Semi-ATE/PCB-Tester/hardware/mechanics/solidworks/2019SP3.0/PCB-Relay-Board/README.md

# PCB-Relay-Board

This directory holds the 3D model of the PCB-Relay-Board (extracted from Altium, or maunally made in solidworks)
