Semi-ATE/PCB-Tester/hardware/mechanics/solidworks/2019SP3.0/PCB-Tester-Board/Raspberry Pi 4B/RPI4B.SLDASM

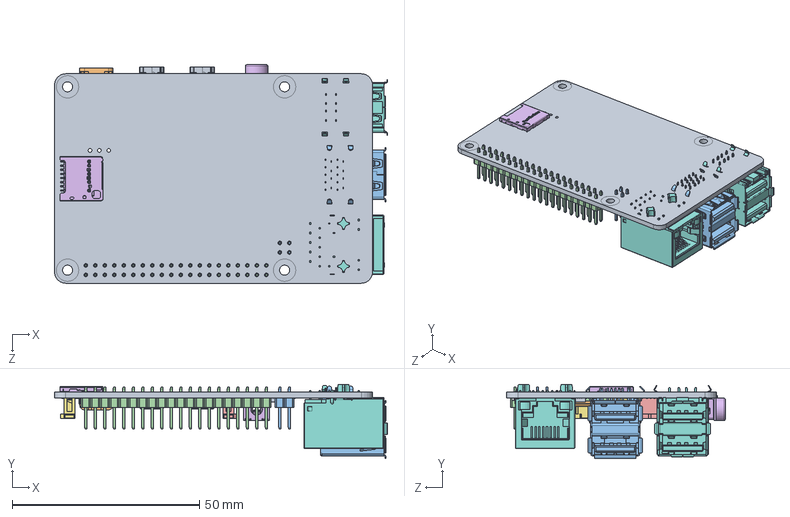
[picture p20: CAD file, 2020-09-08]
hardware/mechanics/solidworks/2019SP3.0/PCB-Tester-Board/Raspberry Pi 4B/RPI4B.SLDASM
89.0 x 19.9 x 58.4 mm
PCB, RPi4ModelB
Broadcom BCM2711B0 CPU, RPi4ModelB
2.54 mm DUPONT MALE PIN HEADER, POE, 2X2, RPi4ModelB
2.54 mm DUPONT MALE PIN HEADER, IO, 2X20, RPi4ModelB
Camera Connector, RPi4ModelB
Microphone Plug, RPi4ModelB
Display Connector, RPi4ModelB
Gigabit Ethernet Port, RPi4ModelB
Female Micro HDMI Connector, RPi4ModelB x 2
Female USB Type C Connector, RPi4ModelB
2X USB3.0 PORTS, RPi4ModelB
91D77 D9WHV 778K, 4 GB LPDDR4 SDRAM, RPi4ModelB
Cypress CYW43455 Wireless Module Cover, RPi4ModelB
SD Card Slot, RPi4ModelB
VIA VL805 PCIe USB 3.0 controller, RPi4ModelB
2X USB2.0 PORTS, RPi4ModelB
Broadcom BCM54213PE Gigabit Ethernet Transceiver, RPi4ModelB
MxL7704 Universal PMIC, RPi4ModelB
