Semi-ATE/PCB-Tester/hardware/mechanics/solidworks/2019SP3.0/housing/Lever_top.SLDASM

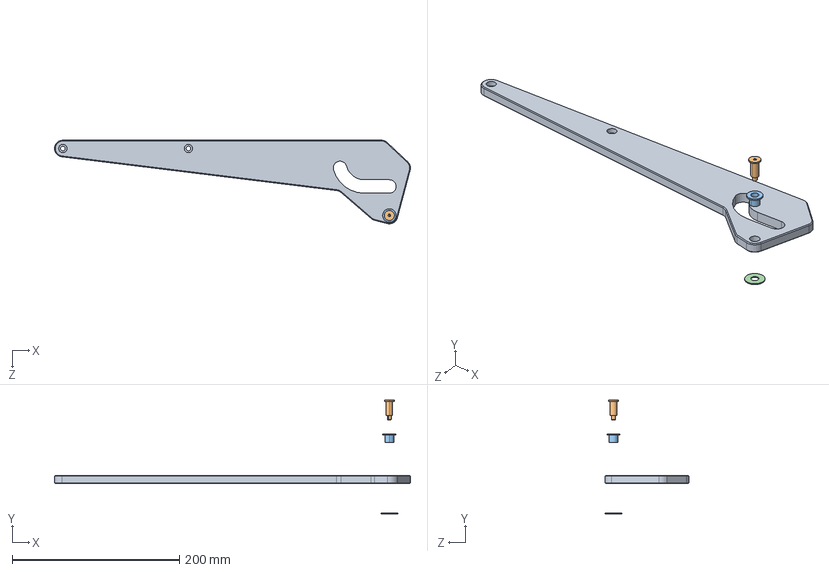
[picture p21: CAD file, 2020-09-08]
hardware/mechanics/solidworks/2019SP3.0/housing/Lever_top.SLDASM
425.2 x 135.8 x 100.0 mm
Lever_top_right
DBGB5-17-5
FWHJ-D10.5-H16.0-V8.0-T1.5-L10.0
SWSJJ20-8-1
