Semi-ATE/PCB-Tester/hardware/mechanics/solidworks/2019SP3.0/housing/Housing.SLDASM

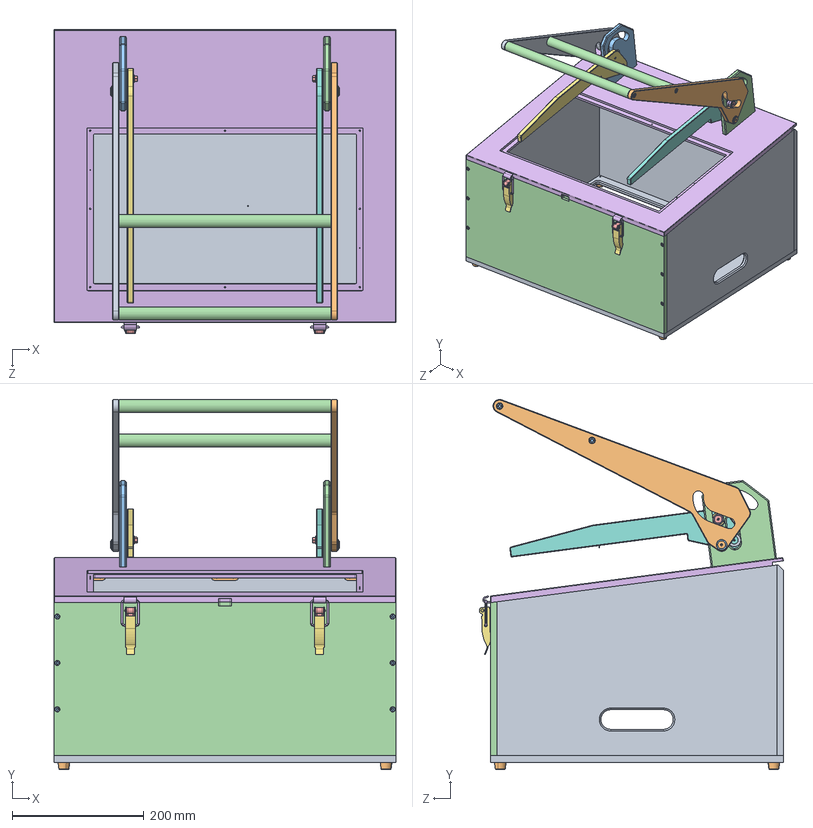
[picture p22: CAD file, 2020-09-08]
hardware/mechanics/solidworks/2019SP3.0/housing/Housing.SLDASM
520.0 x 562.6 x 463.0 mm
Housing_bottom
C-30-RK-18-black x 4
socket head cap screw_iso x 48
Housing_front
420111_base x 2
420111_eye x 2
420111_lever x 2
slotted cheese head screw_iso x 10
Housing_back
SHPSNA5_3 x 3
SHPSNA5_7 x 3
SHPSNA5_5 x 3
hex thin nut gradeb_iso x 6
Housing_top
Lever_bottom_left
Lever_bottom_right
Lever_top_left
Lever_top_right
Spindlehouse_left
Spindlehouse_right
DBGB5-20-10 x 2
B688ZZ x 10
SWSJJ20-8-1 x 6
DBGB5-15-10 x 2
FWHJ-D16.0-H20.0-V8.0-T1.5-L4.0 x 2
DBGB5-17-5 x 2
FWHJ-D10.5-H16.0-V8.0-T1.5-L10.0 x 2
Handle x 2
FRNUT5 x 2
420111_hook x 2
pan head cross recess screw_iso x 4
parallel pin hardened_iso x 4
Housing_side x 2
