Semi-ATE/PCB-Tester/hardware/mechanics/solidworks/2019SP3.0/housing/Spindle3.SLDASM

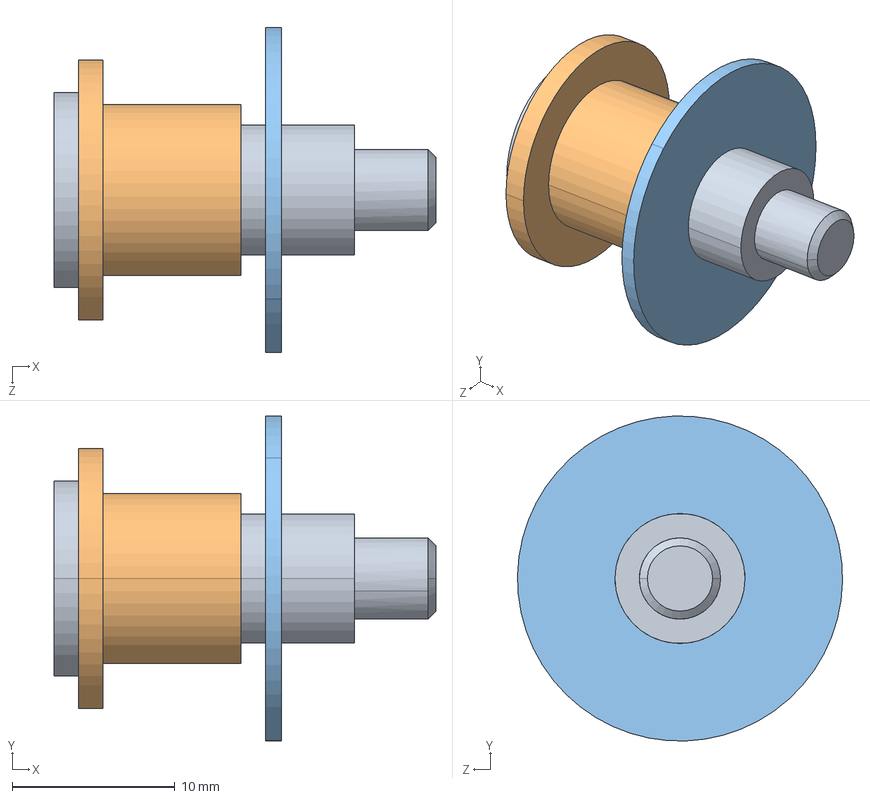
[picture p23: CAD file, 2020-09-08]
hardware/mechanics/solidworks/2019SP3.0/housing/Spindle3.SLDASM
23.5 x 20.0 x 20.0 mm
DBGB5-17-5
FWHJ-D10.5-H16.0-V8.0-T1.5-L10.0
SWSJJ20-8-1
