Semi-ATE/PCB-Tester/hardware/mechanics/solidworks/2019SP3.0/housing/Spindle2.SLDASM

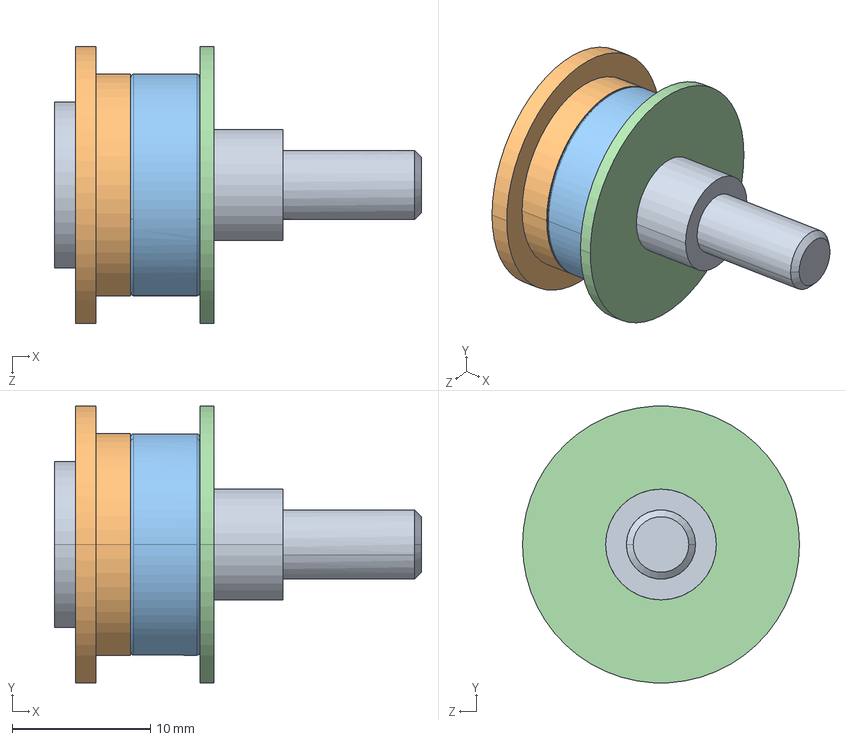
[picture p24: CAD file, 2020-09-08]
hardware/mechanics/solidworks/2019SP3.0/housing/Spindle2.SLDASM
26.5 x 20.0 x 20.0 mm
DBGB5-15-10
FWHJ-D16.0-H20.0-V8.0-T1.5-L4.0
B688ZZ
SWSJJ20-8-1
