Semi-ATE/PCB-Tester/hardware/mechanics/solidworks/2019SP3.0/housing/Lever_bottom.SLDASM

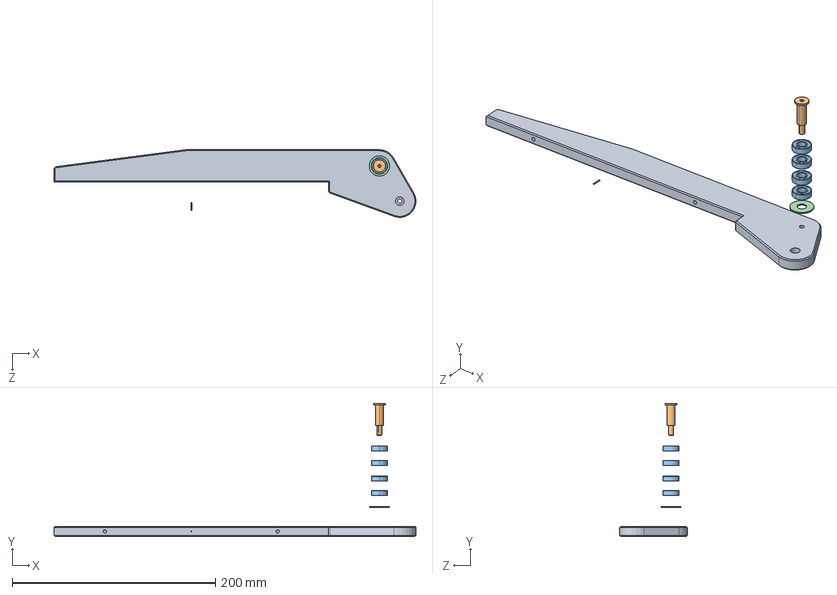
[picture p25: CAD file, 2020-09-08]
hardware/mechanics/solidworks/2019SP3.0/housing/Lever_bottom.SLDASM
356.0 x 130.8 x 66.6 mm
Lever_bottom_right
DBGB5-20-10
B688ZZ x 4
SWSJJ20-8-1
parallel pin hardened_iso
