Semi-ATE/PCB-Tester/hardware/mechanics/solidworks/2019SP3.0/housing/Spindle1.SLDASM

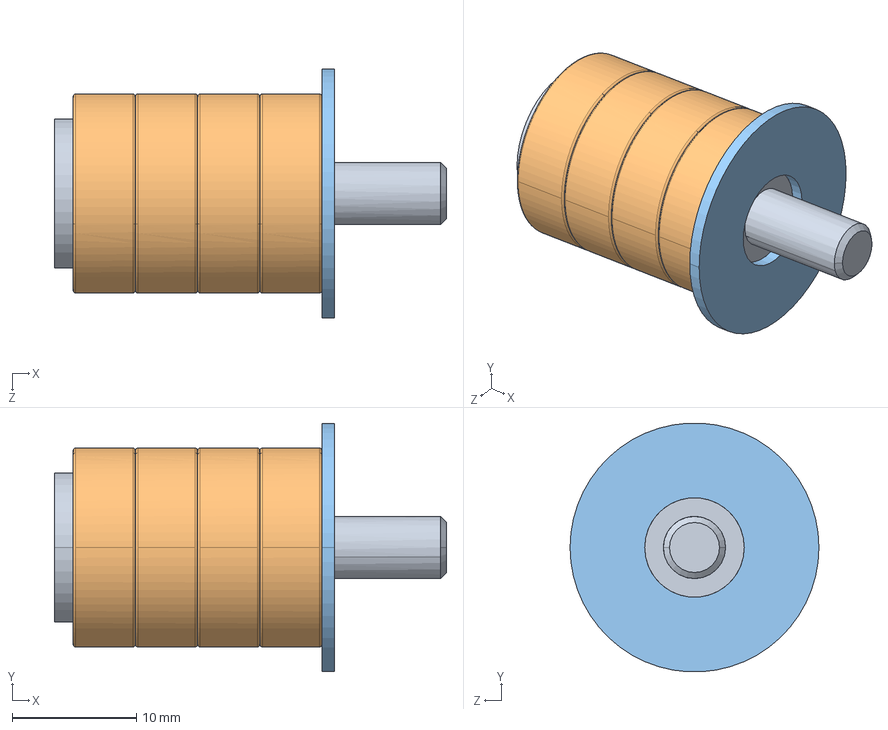
[picture p26: CAD file, 2020-09-08]
hardware/mechanics/solidworks/2019SP3.0/housing/Spindle1.SLDASM
31.5 x 20.0 x 20.0 mm
DBGB5-20-10
B688ZZ x 4
SWSJJ20-8-1
