Semi-ATE/PCB-Tester/hardware/mechanics/solidworks/2019SP3.0/housing/Spindlehouse.SLDASM

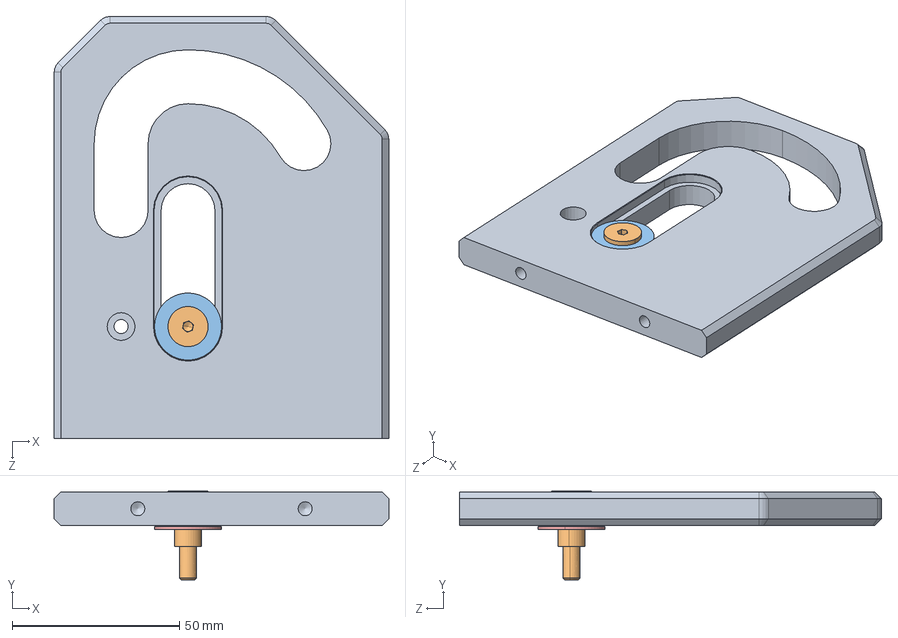
[picture p27: CAD file, 2020-09-08]
hardware/mechanics/solidworks/2019SP3.0/housing/Spindlehouse.SLDASM
100.0 x 26.5 x 126.1 mm
Spindlehouse_right
DBGB5-15-10
FWHJ-D16.0-H20.0-V8.0-T1.5-L4.0
B688ZZ
SWSJJ20-8-1
