Semi-ATE/PCB-Tester/hardware/electronics/altium/20.1.12/PCB-Tester-Board/Parts/SupportPost.STEP

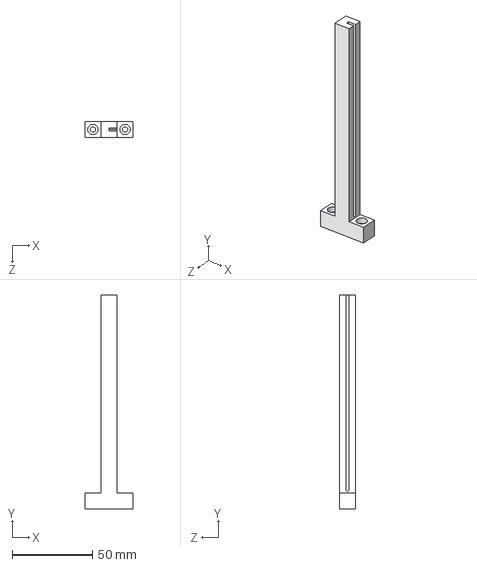
[picture p28: CAD file, 2020-09-08]
hardware/electronics/altium/20.1.12/PCB-Tester-Board/Parts/SupportPost.STEP
30.0 x 133.0 x 10.0 mm
