Semi-ATE/PCB-Tester/hardware/electronics/altium/20.1.12/PCB-Tester-Board/PCB-Tester-Board.DXF

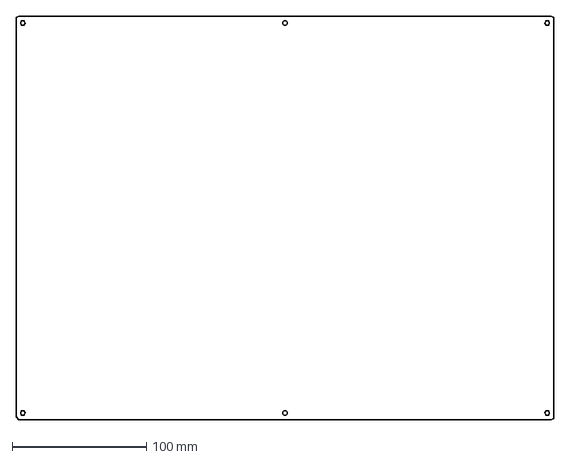
[picture p29: CAD file, 2020-04-20]
hardware/electronics/altium/20.1.12/PCB-Tester-Board/PCB-Tester-Board.DXF
400.0 x 300.0 mm
