Semi-ATE/PCB-Tester/hardware/electronics/altium/20.1.12/PCB-Tester-Relay-Board/Board-Outline.DXF

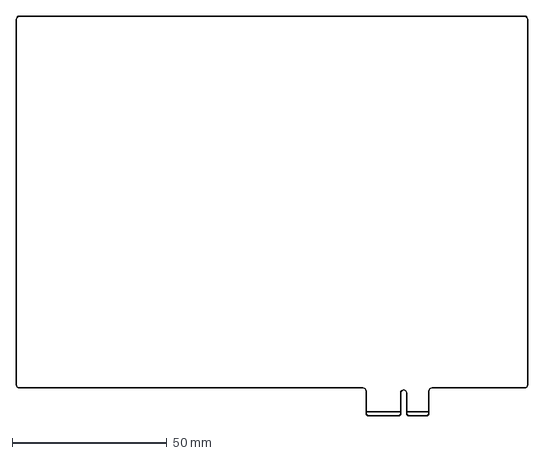
[picture p30: CAD file, 2020-04-20]
hardware/electronics/altium/20.1.12/PCB-Tester-Relay-Board/Board-Outline.DXF
165.0 x 129.0 mm
