Semi-ATE/PCB-Tester/hardware/mechanics/solidworks/2019SP3.0/housing/A22NE-M-PD22-N/A22NE_M_N_BASE.SLDPRT

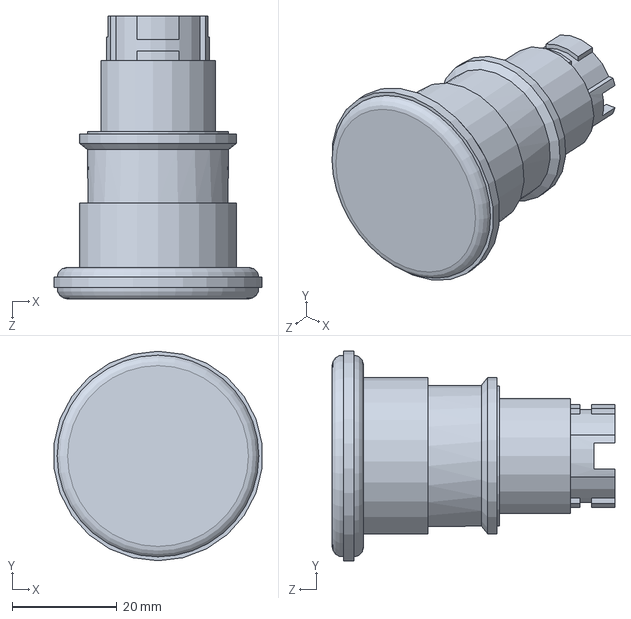
[picture p31: CAD file, 2020-09-11]
hardware/mechanics/solidworks/2019SP3.0/housing/A22NE-M-PD22-N/A22NE_M_N_BASE.SLDPRT
39.7 x 40.0 x 54.0 mm
