Semi-ATE/PCB-Tester/hardware/mechanics/solidworks/2019SP3.0/HUMAN BODY.SLDPRT

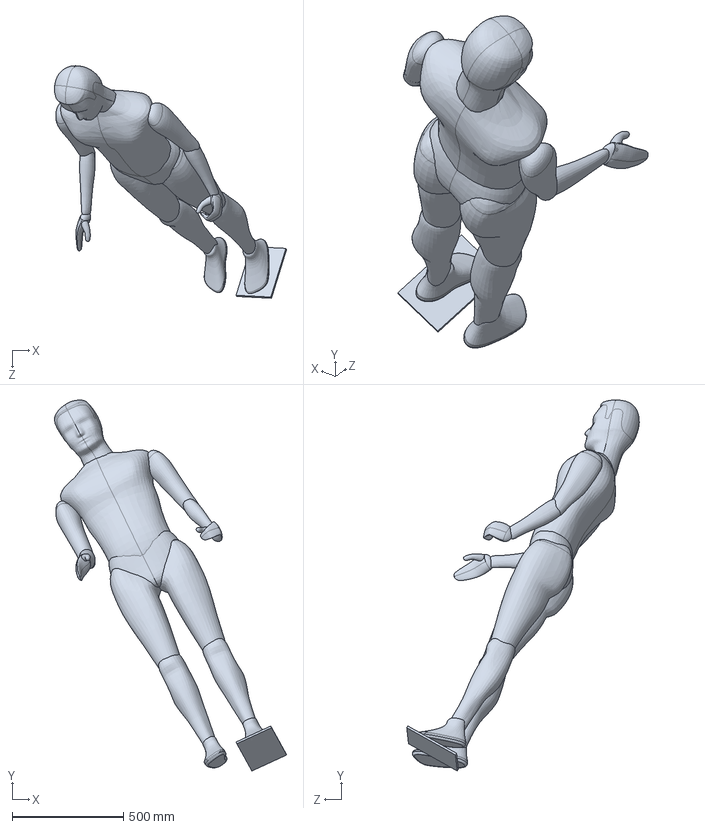
[picture p32: CAD file, 2020-09-08]
hardware/mechanics/solidworks/2019SP3.0/HUMAN BODY.SLDPRT
1042.4 x 1665.2 x 1043.8 mm
