Semi-ATE/PCB-Tester/hardware/mechanics/solidworks/2019SP3.0/PCB-Relay-Board/TFC-132-01-F-D-RA/_TFC_132_01_L_D_RA_terminal_2.sldprt

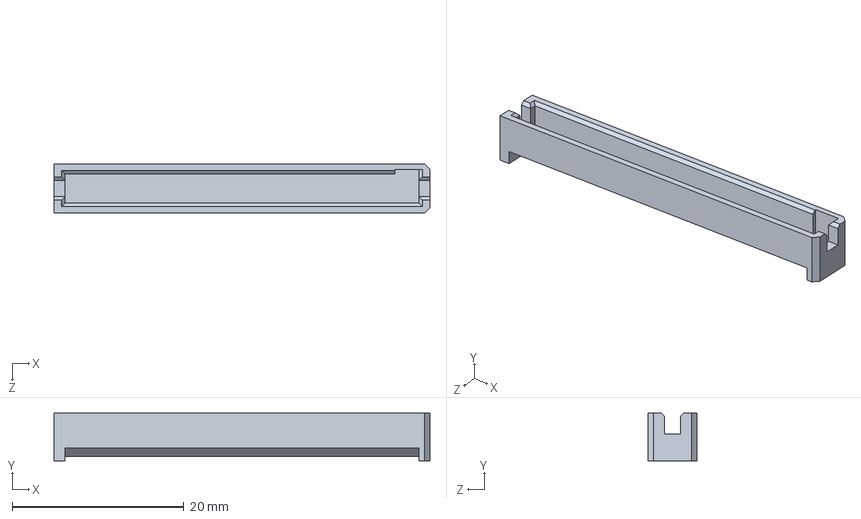
[picture p33: CAD file, 2020-04-20]
hardware/mechanics/solidworks/2019SP3.0/PCB-Relay-Board/TFC-132-01-F-D-RA/_TFC_132_01_L_D_RA_terminal_2.sldprt
43.8 x 5.59 x 5.72 mm
