Semi-ATE/PCB-Tester/hardware/mechanics/solidworks/2019SP3.0/PCB-Tester-Board/118-1-A/118-1-A.SLDPRT

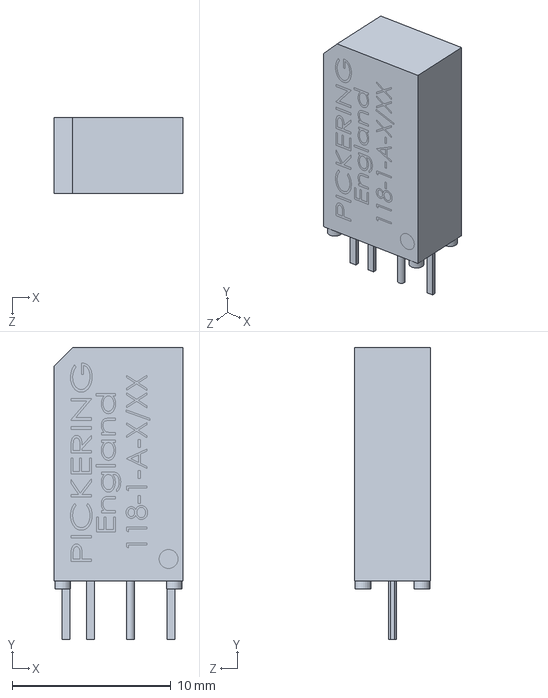
[picture p34: CAD file, 2020-09-08]
hardware/mechanics/solidworks/2019SP3.0/PCB-Tester-Board/118-1-A/118-1-A.SLDPRT
8.13 x 18.4 x 4.80 mm
