Semi-ATE/PCB-Tester/hardware/mechanics/solidworks/2019SP3.0/PCB-Tester-Board/1731721/pxc_1731721_05_GMKDS-3-2-7-62_3D.stp

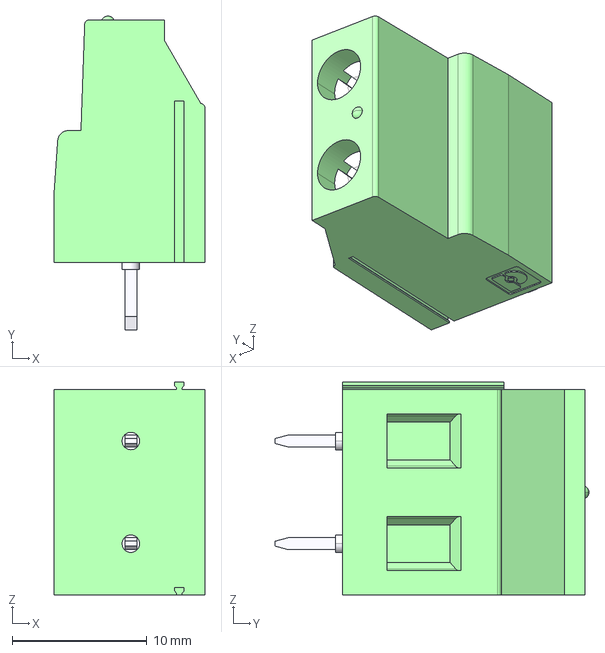
[picture p35: CAD file, 2020-09-08]
hardware/mechanics/solidworks/2019SP3.0/PCB-Tester-Board/1731721/pxc_1731721_05_GMKDS-3-2-7-62_3D.stp
11.2 x 23.3 x 15.8 mm
