Semi-ATE/PCB-Tester/hardware/mechanics/solidworks/2019SP3.0/PCB-Tester-Board/ASE-25.000MHZ-LC-T/ASE.STEP

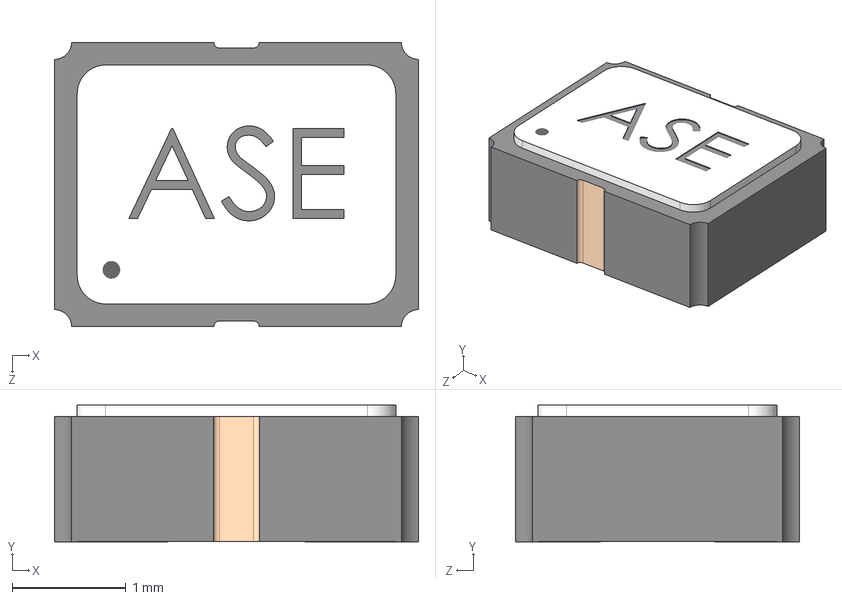
[picture p36: CAD file, 2020-04-20]
hardware/mechanics/solidworks/2019SP3.0/PCB-Tester-Board/ASE-25.000MHZ-LC-T/ASE.STEP
3.20 x 1.20 x 2.50 mm
