Semi-ATE/PCB-Tester/hardware/mechanics/solidworks/2019SP3.0/PCB-Tester-Board/B6PS-VH/VHR-6N.SLDPRT

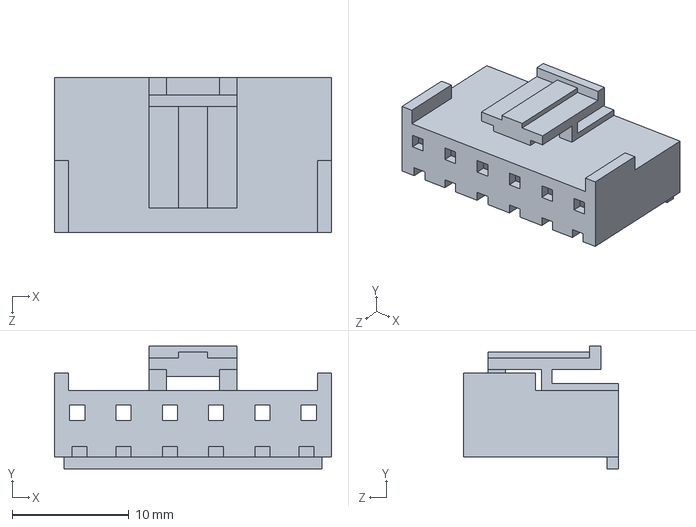
[picture p37: CAD file, 2020-09-08]
hardware/mechanics/solidworks/2019SP3.0/PCB-Tester-Board/B6PS-VH/VHR-6N.SLDPRT
23.7 x 10.5 x 13.3 mm
