Semi-ATE/PCB-Tester/hardware/mechanics/solidworks/2019SP3.0/PCB-Tester-Board/G3VM-61A1/G3VM_61A1.STEP

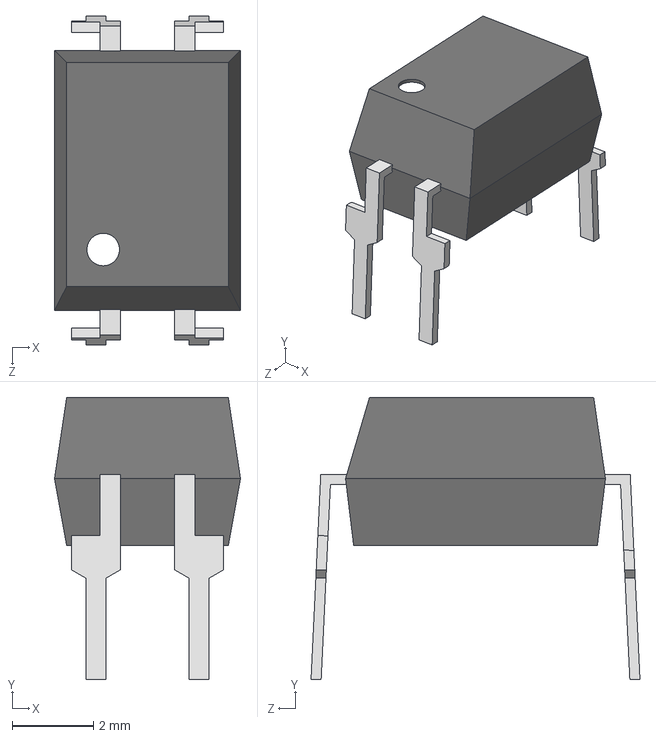
[picture p38: CAD file, 2020-04-20]
hardware/mechanics/solidworks/2019SP3.0/PCB-Tester-Board/G3VM-61A1/G3VM_61A1.STEP
4.58 x 6.95 x 8.10 mm
