Semi-ATE/PCB-Tester/hardware/mechanics/solidworks/2019SP3.0/PCB-Tester-Board/HF118F005-1ZS1/HF118F005-1ZS1.STEP

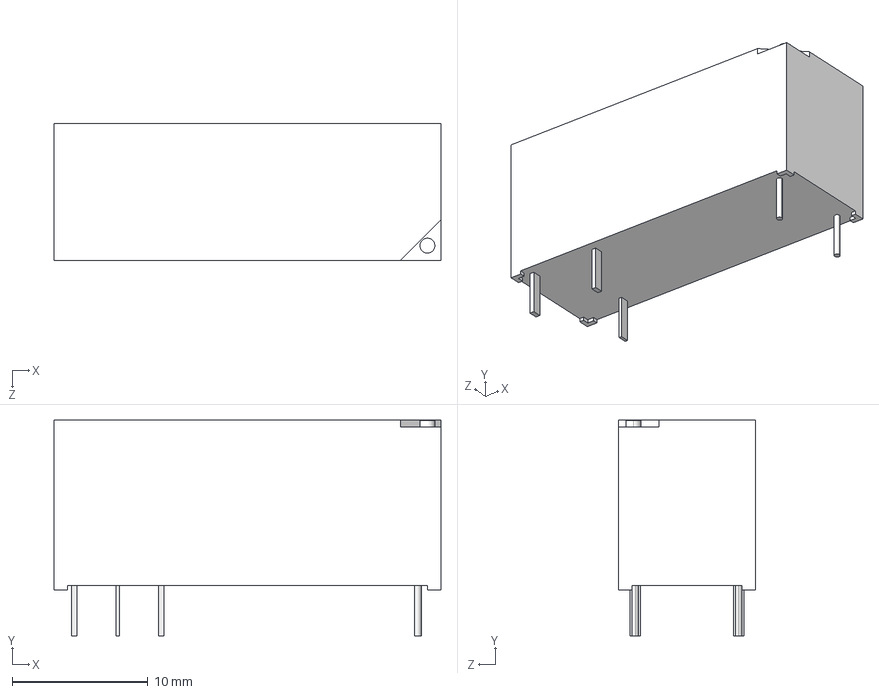
[picture p39: CAD file, 2020-04-20]
hardware/mechanics/solidworks/2019SP3.0/PCB-Tester-Board/HF118F005-1ZS1/HF118F005-1ZS1.STEP
28.5 x 15.9 x 10.1 mm
