Semi-ATE/PCB-Tester/hardware/mechanics/solidworks/2019SP3.0/PCB-Tester-Board/PCB-Tester-PCB.SLDPRT

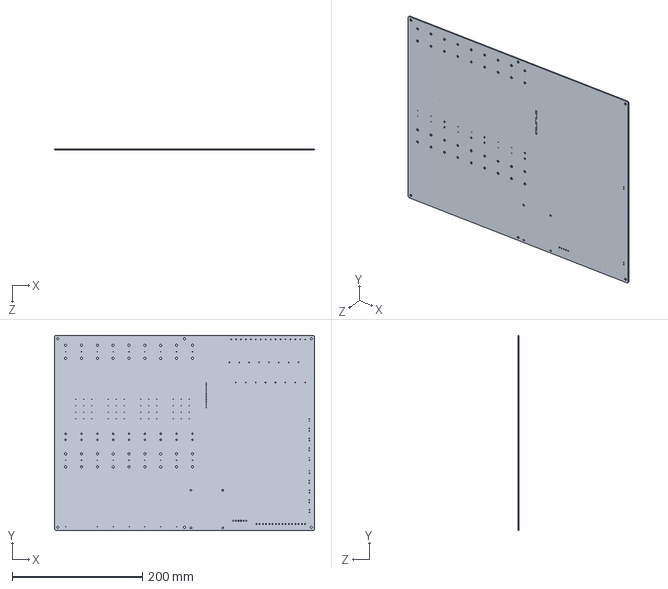
[picture p40: CAD file, 2020-09-08]
hardware/mechanics/solidworks/2019SP3.0/PCB-Tester-Board/PCB-Tester-PCB.SLDPRT
400.0 x 300.0 x 1.60 mm
