Semi-ATE/PCB-Tester/hardware/mechanics/solidworks/2019SP3.0/PCB-Tester-Board/TFC-132-01-F-D-LC/TFC-132-01-F-D-LC.STEP

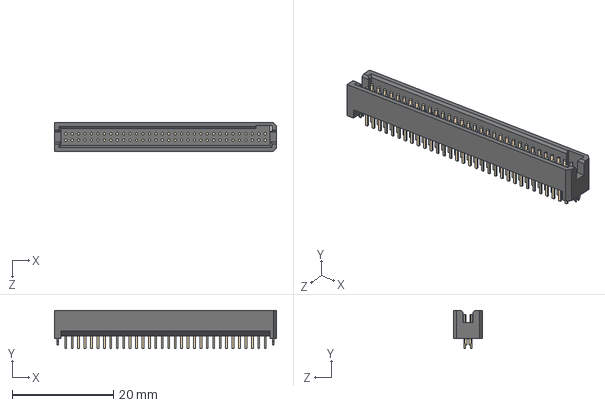
[picture p42: CAD file, 2020-04-20]
hardware/mechanics/solidworks/2019SP3.0/PCB-Tester-Board/TFC-132-01-F-D-LC/TFC-132-01-F-D-LC.STEP
43.8 x 7.57 x 5.71 mm
_TFC_132_01_L_D_LC_terminal_2
_TFC_132_01_L_D_pins_4
