Semi-ATE/PCB-Tester/hardware/mechanics/solidworks/2019SP3.0/PCB-Tester-Board/TSR 2-2450/TSR2-2405.STEP

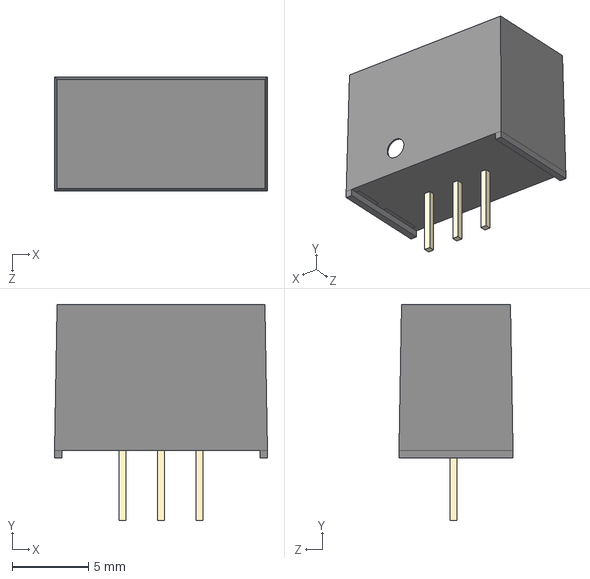
[picture p43: CAD file, 2020-04-20]
hardware/mechanics/solidworks/2019SP3.0/PCB-Tester-Board/TSR 2-2450/TSR2-2405.STEP
14.0 x 14.2 x 7.50 mm
