Semi-ATE/PCB-Tester/hardware/electronics/altium/20.1.12/PCB-Tester-Board/Parts/SupportBlock.STEP

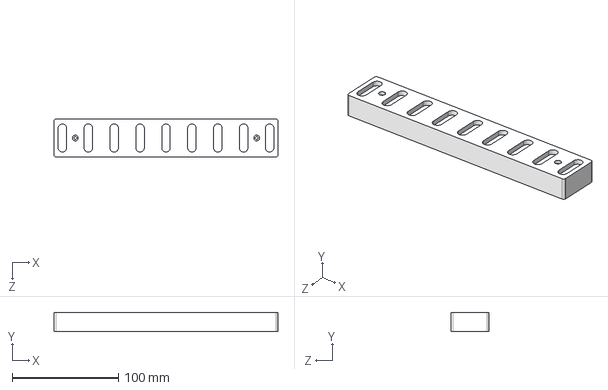
[picture p44: CAD file, 2020-09-08]
hardware/electronics/altium/20.1.12/PCB-Tester-Board/Parts/SupportBlock.STEP
211.0 x 18.0 x 36.0 mm
