Semi-ATE/PCB-Tester/hardware/mechanics/solidworks/2019SP3.0/housing/Housing_side.STEP

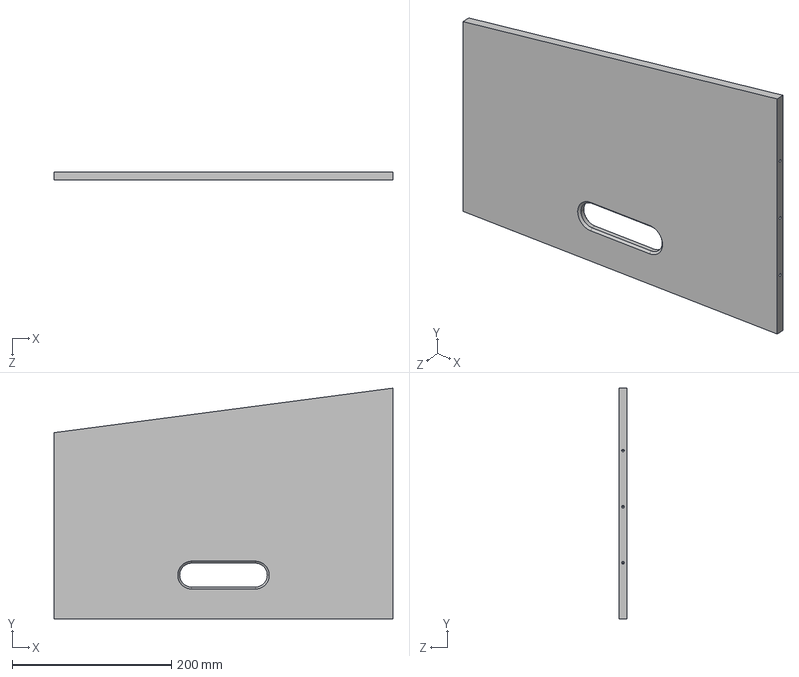
[picture p45: CAD file, 2020-09-11]
hardware/mechanics/solidworks/2019SP3.0/housing/Housing_side.STEP
426.0 x 290.0 x 10.0 mm
