Semi-ATE/PCB-Tester/hardware/mechanics/solidworks/2019SP3.0/housing/NP8E2D203QE/NP8E2D203QE_3.sldprt

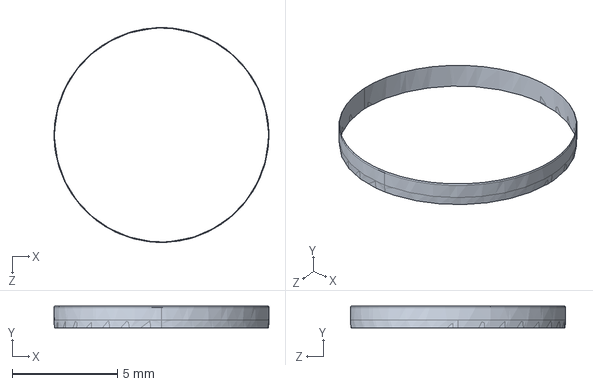
[picture p46: CAD file, 2020-09-11]
hardware/mechanics/solidworks/2019SP3.0/housing/NP8E2D203QE/NP8E2D203QE_3.sldprt
10.2 x 1.03 x 10.2 mm
