Semi-ATE/PCB-Tester/hardware/mechanics/solidworks/2019SP3.0/PCB-Relay-Board/PCB-Relay-PCB.SLDPRT

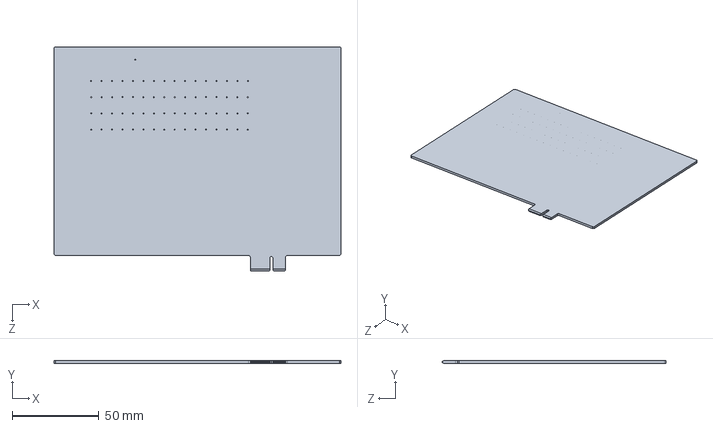
[picture p47: CAD file, 2020-09-08]
hardware/mechanics/solidworks/2019SP3.0/PCB-Relay-Board/PCB-Relay-PCB.SLDPRT
165.0 x 1.60 x 129.0 mm
