Semi-ATE/PCB-Tester/hardware/mechanics/solidworks/2019SP3.0/PCB-Relay-Board/SFSD-32-30C-G-15.00-S/_SFSD_32_28_D_NUS_ca_4.sldprt

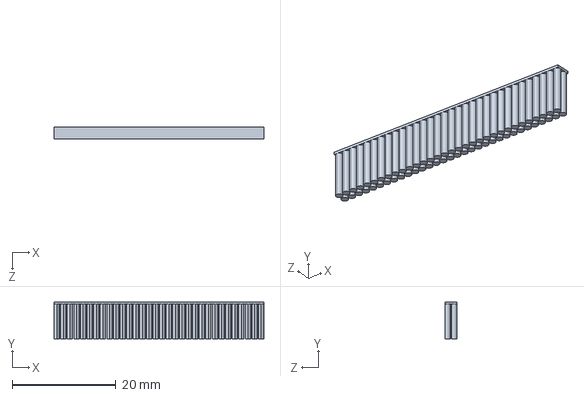
[picture p48: CAD file, 2020-04-20]
hardware/mechanics/solidworks/2019SP3.0/PCB-Relay-Board/SFSD-32-30C-G-15.00-S/_SFSD_32_28_D_NUS_ca_4.sldprt
40.4 x 7.11 x 2.34 mm
