Semi-ATE/PCB-Tester/hardware/mechanics/solidworks/2019SP3.0/PCB-Relay-Board/TFC-132-01-F-D-RA/TFC-132-01-F-D-RA.STEP

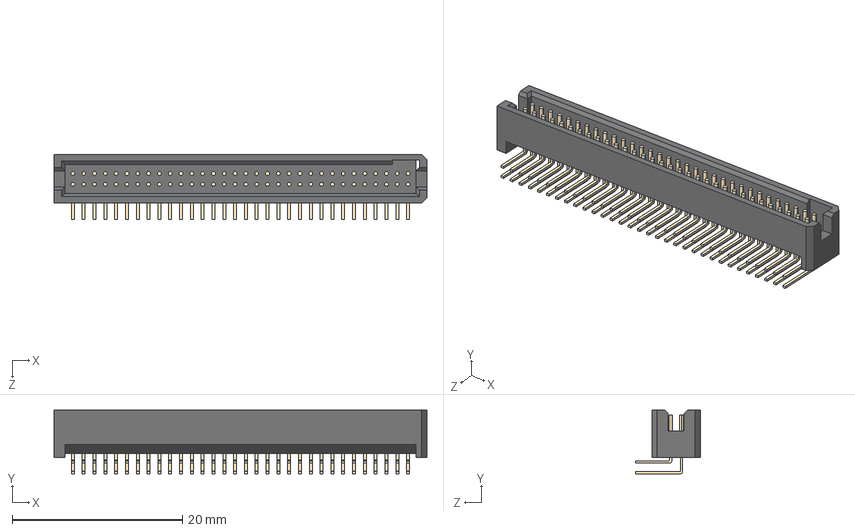
[picture p49: CAD file, 2020-04-20]
hardware/mechanics/solidworks/2019SP3.0/PCB-Relay-Board/TFC-132-01-F-D-RA/TFC-132-01-F-D-RA.STEP
43.8 x 7.49 x 7.62 mm
_TFC_132_01_L_D_RA_terminal_2
_TFC_132_01_L_D_RA_pins_4
