Semi-ATE/PCB-Tester/hardware/mechanics/solidworks/2019SP3.0/PCB-Tester-Board/M2.5x16 standoff/HSM2.5-6.4-16-2.STEP

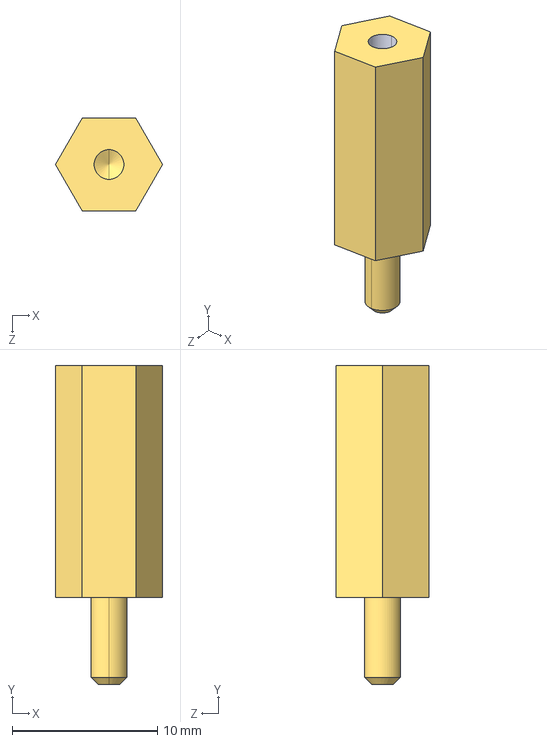
[picture p50: CAD file, 2020-04-20]
hardware/mechanics/solidworks/2019SP3.0/PCB-Tester-Board/M2.5x16 standoff/HSM2.5-6.4-16-2.STEP
7.39 x 22.0 x 6.40 mm
