Semi-ATE/PCB-Tester/hardware/mechanics/solidworks/2019SP3.0/PCB-Tester-Board/PCIE-036-02-F-D-TH/PCIE_036_02_F_D_TH_3.sldprt

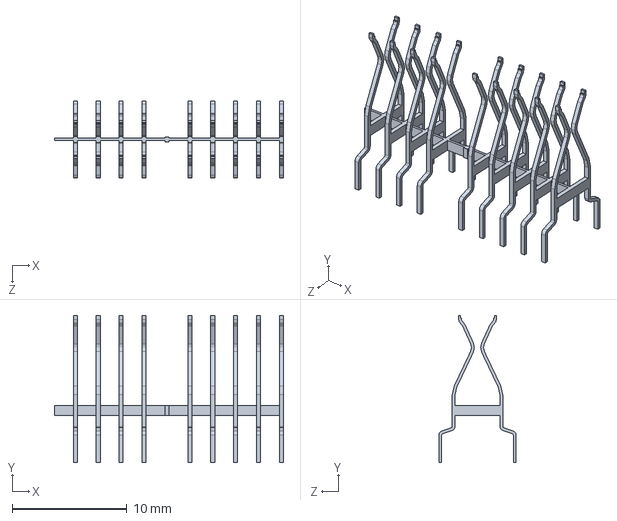
[picture p51: CAD file, 2020-09-08]
hardware/mechanics/solidworks/2019SP3.0/PCB-Tester-Board/PCIE-036-02-F-D-TH/PCIE_036_02_F_D_TH_3.sldprt
20.0 x 12.9 x 6.76 mm
