Semi-ATE/PCB-Tester/hardware/mechanics/solidworks/2019SP3.0/PCB-Tester-Board/TFC-132-01-F-D-LC/_TFC_132_01_L_D_LC_terminal_2.sldprt

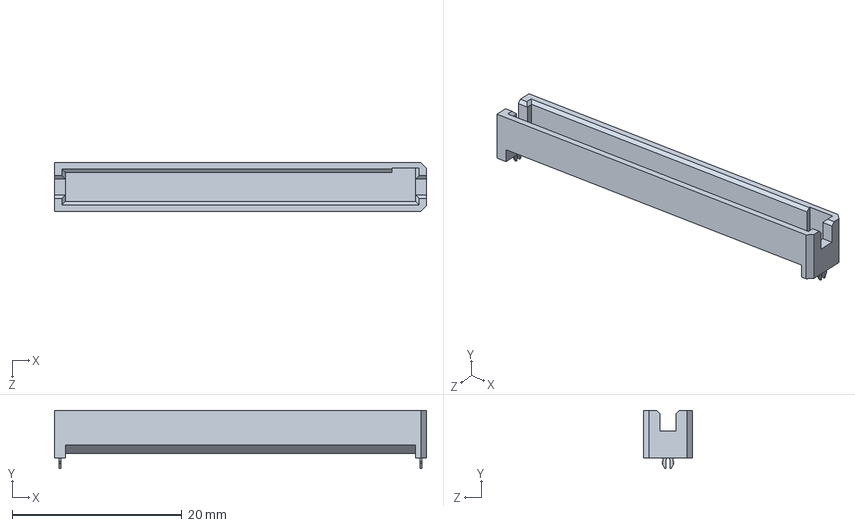
[picture p53: CAD file, 2020-04-20]
hardware/mechanics/solidworks/2019SP3.0/PCB-Tester-Board/TFC-132-01-F-D-LC/_TFC_132_01_L_D_LC_terminal_2.sldprt
43.8 x 6.86 x 5.72 mm
