Semi-ATE/PCB-Tester/hardware/mechanics/solidworks/2019SP3.0/housing/Housing_bottom.STEP

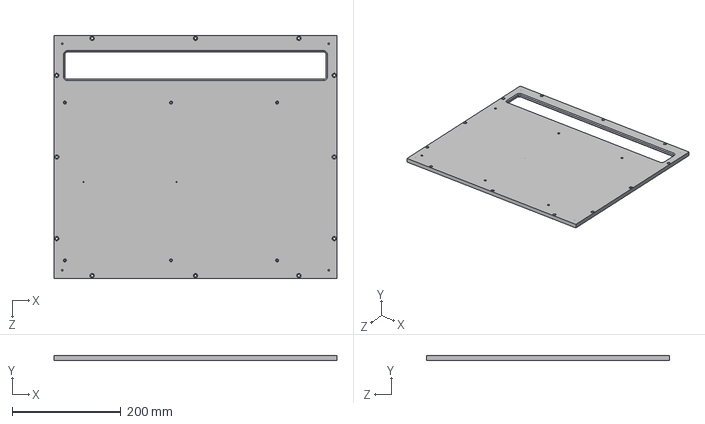
[picture p54: CAD file, 2020-09-11]
hardware/mechanics/solidworks/2019SP3.0/housing/Housing_bottom.STEP
520.0 x 10.0 x 446.0 mm
