Semi-ATE/PCB-Tester/hardware/mechanics/solidworks/2019SP3.0/PCB-Relay-Board/SFSD-32-30C-G-15.00-S/_SFSD_32_30_S_b_2.sldprt

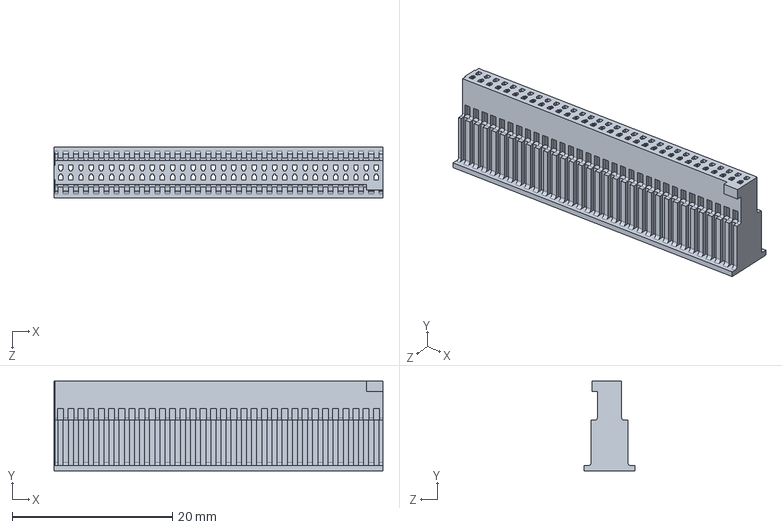
[picture p55: CAD file, 2020-04-20]
hardware/mechanics/solidworks/2019SP3.0/PCB-Relay-Board/SFSD-32-30C-G-15.00-S/_SFSD_32_30_S_b_2.sldprt
41.0 x 11.2 x 6.35 mm
