Semi-ATE/PCB-Tester/hardware/mechanics/solidworks/2019SP3.0/PCB-Relay-Board/TFC-132-01-F-D-RA/_TFC_132_01_L_D_RA_pins_4.sldprt

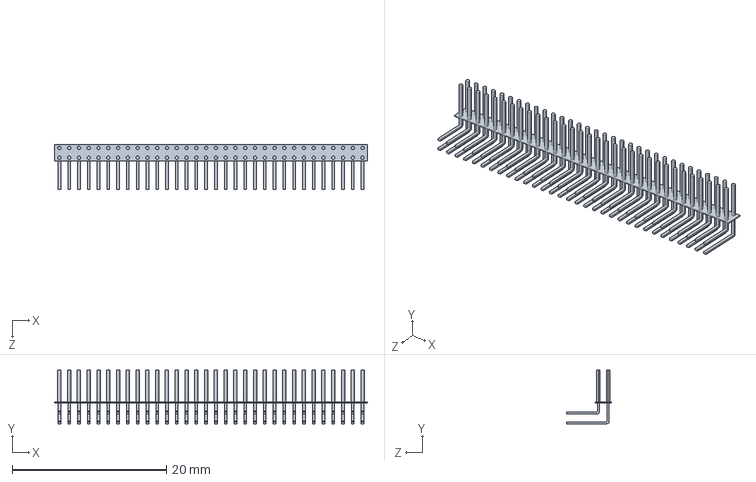
[picture p56: CAD file, 2020-04-20]
hardware/mechanics/solidworks/2019SP3.0/PCB-Relay-Board/TFC-132-01-F-D-RA/_TFC_132_01_L_D_RA_pins_4.sldprt
40.6 x 6.95 x 5.84 mm
