Semi-ATE/PCB-Tester/hardware/mechanics/solidworks/2019SP3.0/PCB-Tester-Board/TFC-132-01-F-D-LC/_TFC_132_01_L_D_pins_4.sldprt

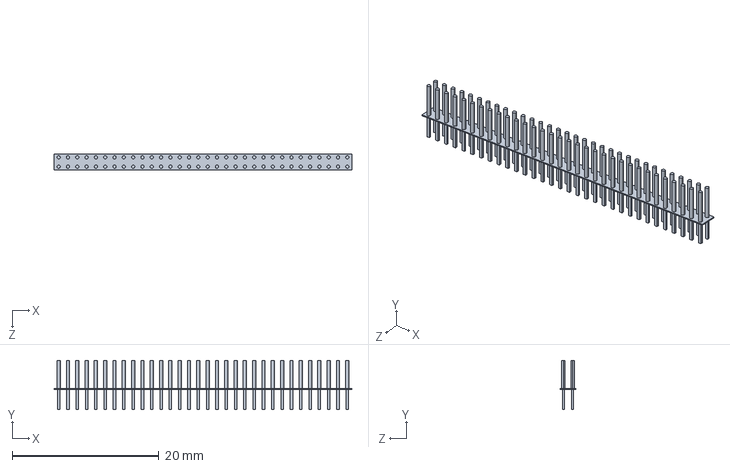
[picture p59: CAD file, 2020-04-20]
hardware/mechanics/solidworks/2019SP3.0/PCB-Tester-Board/TFC-132-01-F-D-LC/_TFC_132_01_L_D_pins_4.sldprt
40.6 x 6.74 x 2.16 mm
