Semi-ATE/PCB-Tester/hardware/mechanics/solidworks/2019SP3.0/housing/Housing_front.STEP

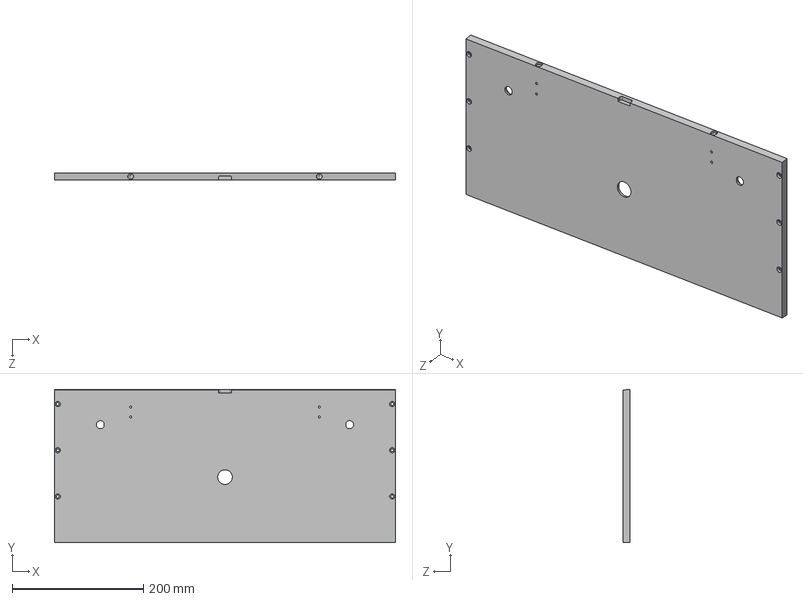
[picture p60: CAD file, 2020-09-11]
hardware/mechanics/solidworks/2019SP3.0/housing/Housing_front.STEP
520.0 x 234.0 x 10.0 mm
