Semi-ATE/PCB-Tester/hardware/mechanics/solidworks/2019SP3.0/housing/NP8E2D203QE/NP8E2D203QE_11.sldprt

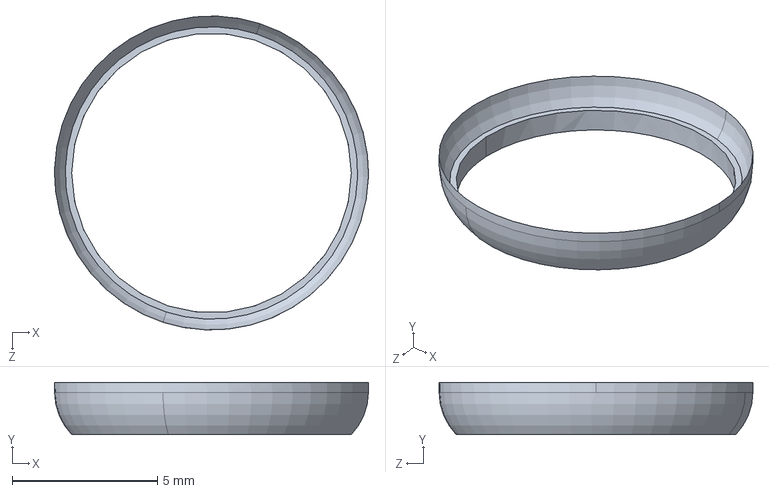
[picture p61: CAD file, 2020-09-11]
hardware/mechanics/solidworks/2019SP3.0/housing/NP8E2D203QE/NP8E2D203QE_11.sldprt
10.8 x 1.80 x 10.8 mm
