Semi-ATE/PCB-Tester/hardware/mechanics/solidworks/2019SP3.0/JIG/JBH6_10.sldprt

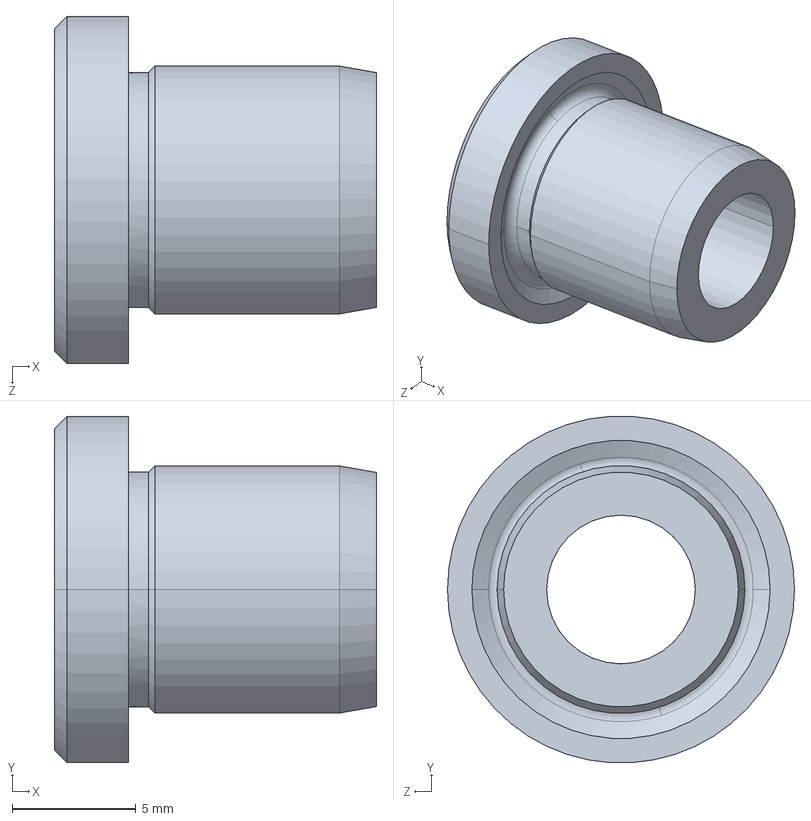
[picture p62: CAD file, 2020-09-08]
hardware/mechanics/solidworks/2019SP3.0/JIG/JBH6_10.sldprt
13.0 x 14.0 x 14.0 mm
