Semi-ATE/PCB-Tester/hardware/mechanics/solidworks/2019SP3.0/PCB-Relay-Board/SFSD-32-30C-G-15.00-S/_SFSD_32_p_6.sldprt

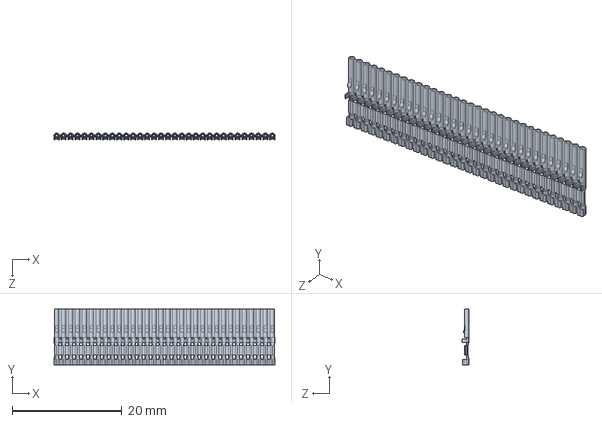
[picture p63: CAD file, 2020-04-20]
hardware/mechanics/solidworks/2019SP3.0/PCB-Relay-Board/SFSD-32-30C-G-15.00-S/_SFSD_32_p_6.sldprt
40.3 x 10.2 x 1.27 mm
