Semi-ATE/PCB-Tester/hardware/mechanics/solidworks/2019SP3.0/PCB-Tester-Board/PCIE-036-02-F-D-TH/PCIE_036_02_F_D_TH_7.sldprt

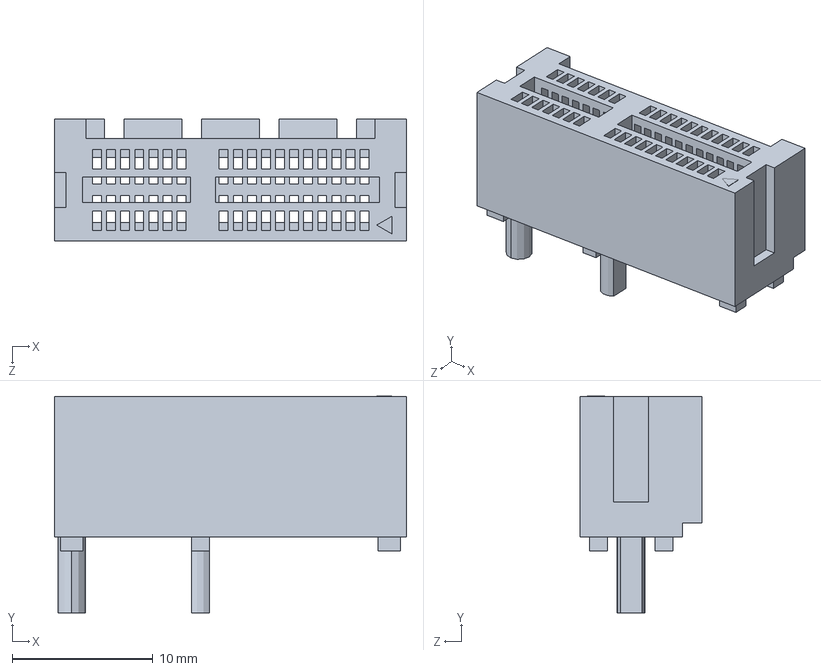
[picture p64: CAD file, 2020-09-08]
hardware/mechanics/solidworks/2019SP3.0/PCB-Tester-Board/PCIE-036-02-F-D-TH/PCIE_036_02_F_D_TH_7.sldprt
25.0 x 15.4 x 8.70 mm
