Semi-ATE/PCB-Tester/hardware/mechanics/solidworks/2019SP3.0/PCB-Tester-Board/Raspberry Pi 4B/2.54 mm DUPONT MALE PIN HEADER, IO, 2X20, RPi4ModelB.SLDPRT

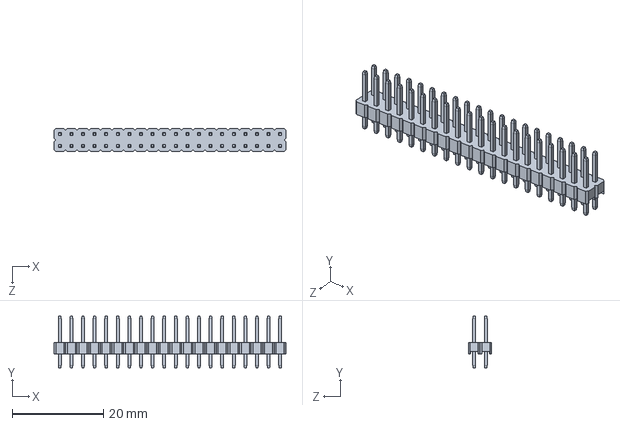
[picture p65: CAD file, 2020-09-08]
hardware/mechanics/solidworks/2019SP3.0/PCB-Tester-Board/Raspberry Pi 4B/2.54 mm DUPONT MALE PIN HEADER, IO, 2X20, RPi4ModelB.SLDPRT
50.8 x 11.3 x 5.08 mm
