Semi-ATE/PCB-Tester/hardware/mechanics/solidworks/2019SP3.0/housing/Housing_top.STEP

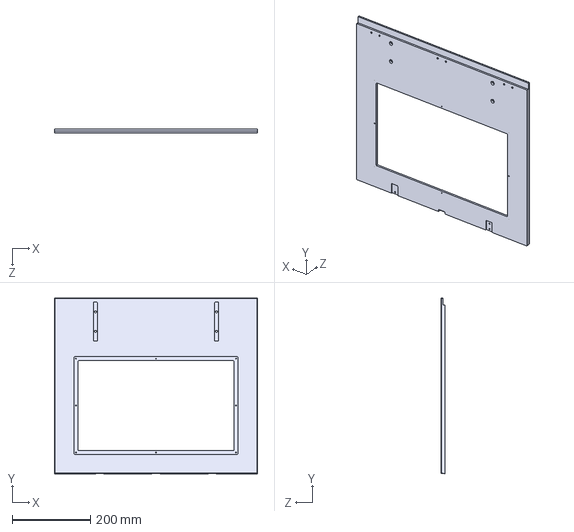
[picture p66: CAD file, 2020-09-11]
hardware/mechanics/solidworks/2019SP3.0/housing/Housing_top.STEP
520.0 x 450.0 x 10.0 mm
