Semi-ATE/PCB-Tester/hardware/mechanics/solidworks/2019SP3.0/PCB-Tester-Board/Raspberry Pi 4B/Broadcom BCM2711B0 CPU, RPi4ModelB.SLDPRT

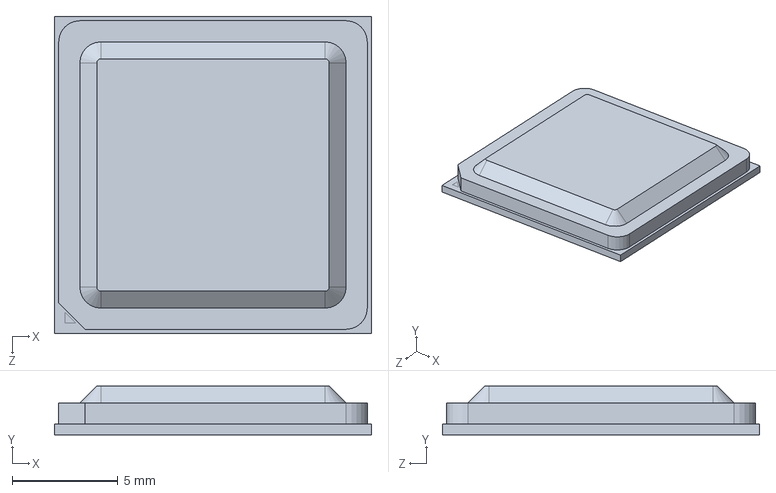
[picture p68: CAD file, 2020-09-08]
hardware/mechanics/solidworks/2019SP3.0/PCB-Tester-Board/Raspberry Pi 4B/Broadcom BCM2711B0 CPU, RPi4ModelB.SLDPRT
15.0 x 2.30 x 15.0 mm
