Semi-ATE/PCB-Tester/hardware/mechanics/solidworks/2019SP3.0/housing/A22NE-M-PD22-N/A22NE_M_PD22_N_LEVER.SLDPRT

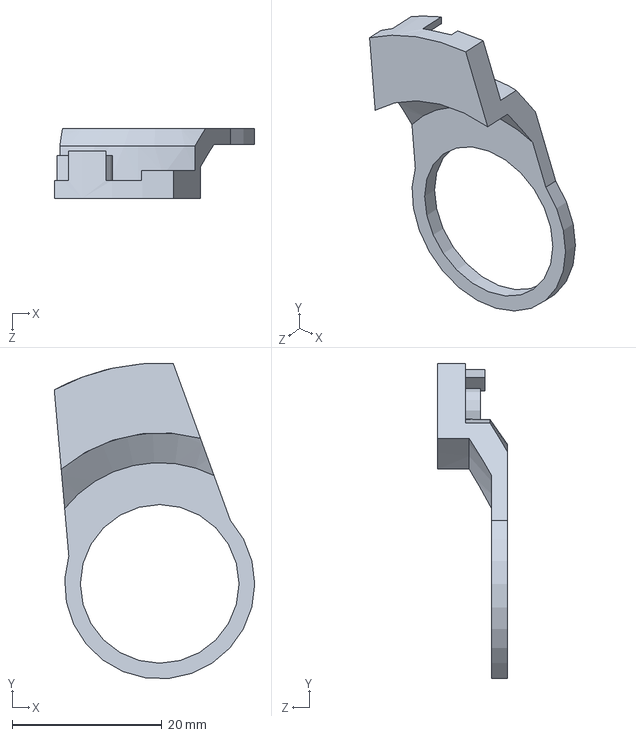
[picture p69: CAD file, 2020-09-11]
hardware/mechanics/solidworks/2019SP3.0/housing/A22NE-M-PD22-N/A22NE_M_PD22_N_LEVER.SLDPRT
26.8 x 42.1 x 9.30 mm
