Semi-ATE/PCB-Tester/hardware/mechanics/solidworks/2019SP3.0/housing/KMF1.1291.11.SLDPRT

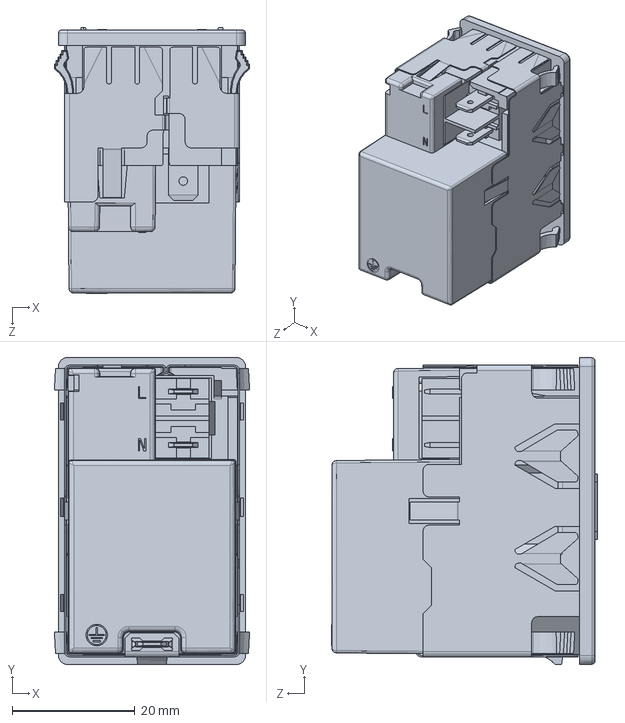
[picture p70: CAD file, 2020-09-11]
hardware/mechanics/solidworks/2019SP3.0/housing/KMF1.1291.11.SLDPRT
31.8 x 50.0 x 43.4 mm
