Semi-ATE/PCB-Tester/hardware/mechanics/solidworks/2019SP3.0/JIG/Cover_short.SLDPRT

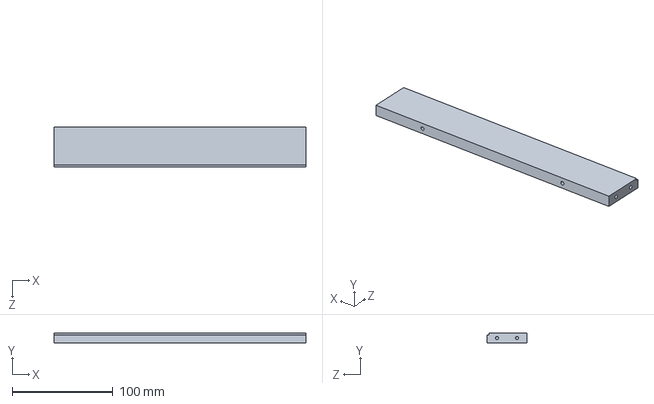
[picture p71: CAD file, 2020-09-08]
hardware/mechanics/solidworks/2019SP3.0/JIG/Cover_short.SLDPRT
250.0 x 10.0 x 40.0 mm
