Semi-ATE/PCB-Tester/hardware/mechanics/solidworks/2019SP3.0/housing/Housing_back.STEP

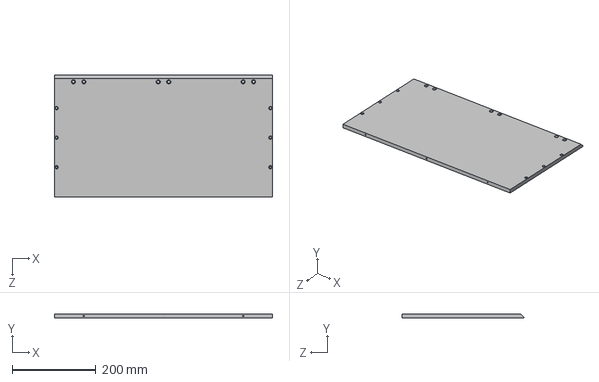
[picture p72: CAD file, 2020-09-08]
hardware/mechanics/solidworks/2019SP3.0/housing/Housing_back.STEP
520.0 x 10.0 x 290.0 mm
