Semi-ATE/PCB-Tester/hardware/mechanics/solidworks/2019SP3.0/housing/NP8E2D203QE/NP8E2D203QE_13.sldprt

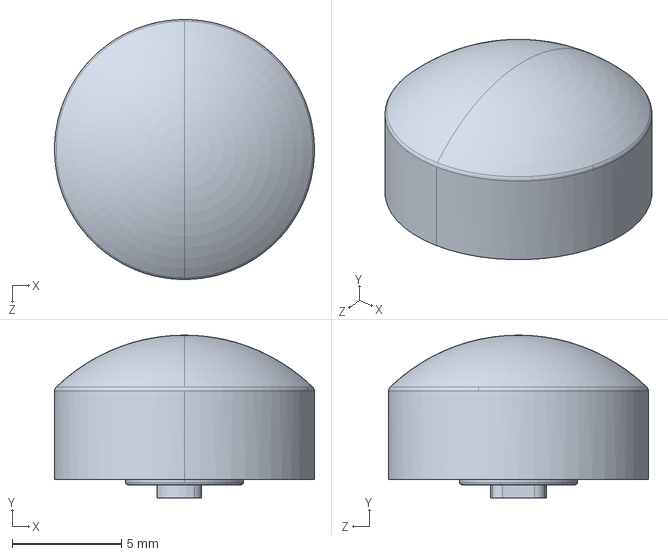
[picture p73: CAD file, 2020-09-11]
hardware/mechanics/solidworks/2019SP3.0/housing/NP8E2D203QE/NP8E2D203QE_13.sldprt
11.9 x 7.45 x 11.9 mm
