Semi-ATE/PCB-Tester/hardware/mechanics/solidworks/2019SP3.0/JIG/SFTF6_55_J5_M3.sldprt

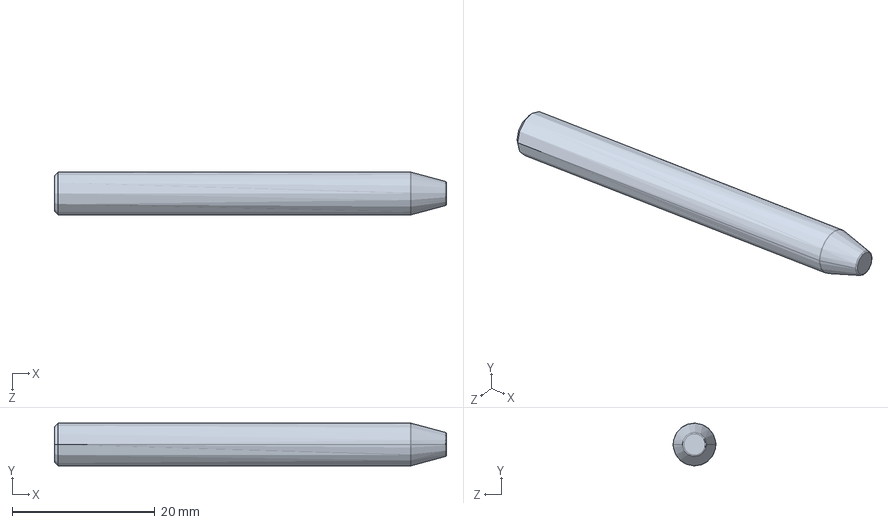
[picture p74: CAD file, 2020-09-08]
hardware/mechanics/solidworks/2019SP3.0/JIG/SFTF6_55_J5_M3.sldprt
55.0 x 6.00 x 6.00 mm
