Semi-ATE/PCB-Tester/hardware/mechanics/solidworks/2019SP3.0/PCB-Tester-Board/Raspberry Pi 4B/PCB, RPi4ModelB.SLDPRT

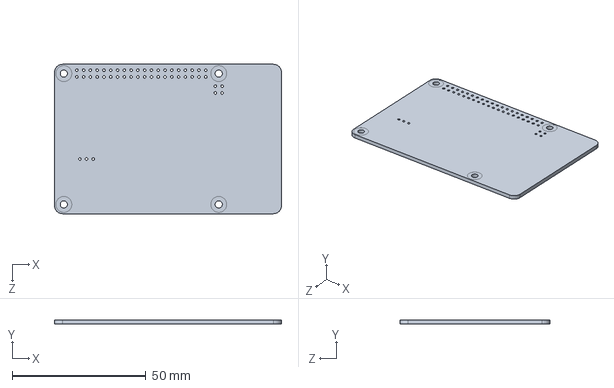
[picture p75: CAD file, 2020-09-08]
hardware/mechanics/solidworks/2019SP3.0/PCB-Tester-Board/Raspberry Pi 4B/PCB, RPi4ModelB.SLDPRT
85.0 x 1.60 x 56.0 mm
