Semi-ATE/PCB-Tester/hardware/mechanics/solidworks/2019SP3.0/housing/Lever_bottom_left.STEP

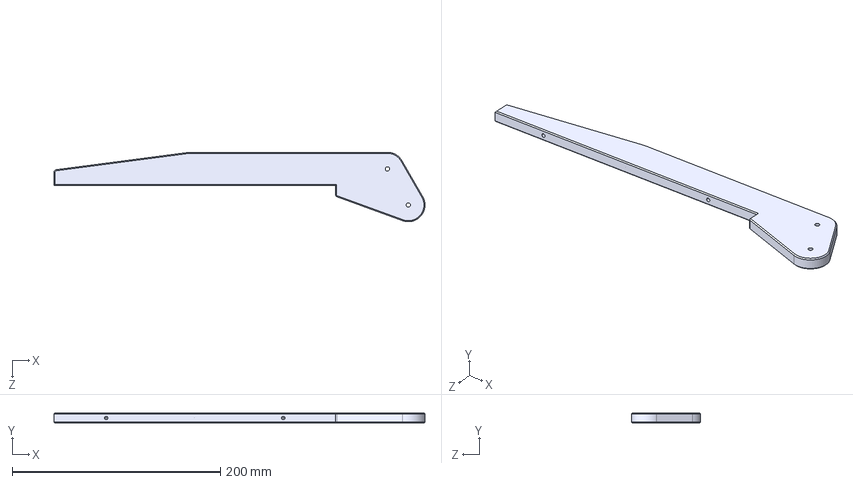
[picture p76: CAD file, 2020-09-08]
hardware/mechanics/solidworks/2019SP3.0/housing/Lever_bottom_left.STEP
356.0 x 10.0 x 66.6 mm
