Semi-ATE/PCB-Tester/hardware/mechanics/solidworks/2019SP3.0/JIG/Cover_top.SLDPRT

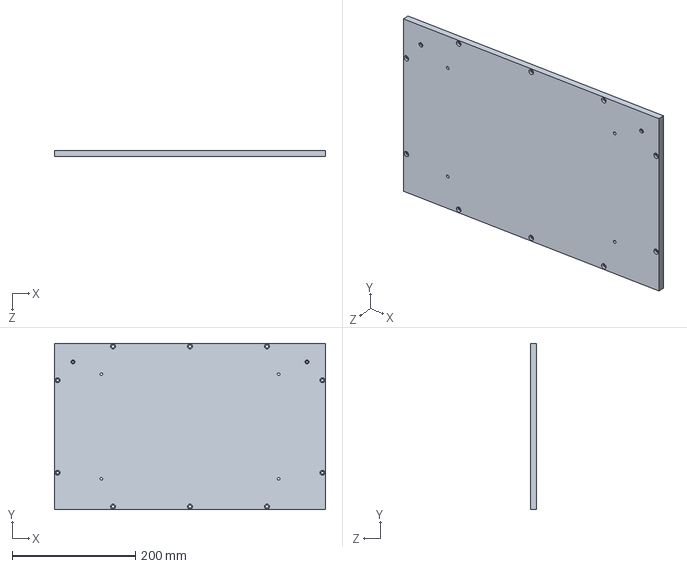
[picture p77: CAD file, 2020-09-08]
hardware/mechanics/solidworks/2019SP3.0/JIG/Cover_top.SLDPRT
440.0 x 270.0 x 10.0 mm
