Semi-ATE/PCB-Tester/hardware/mechanics/solidworks/2019SP3.0/PCB-Tester-Board/Raspberry Pi 4B/Camera Connector, RPi4ModelB.SLDPRT

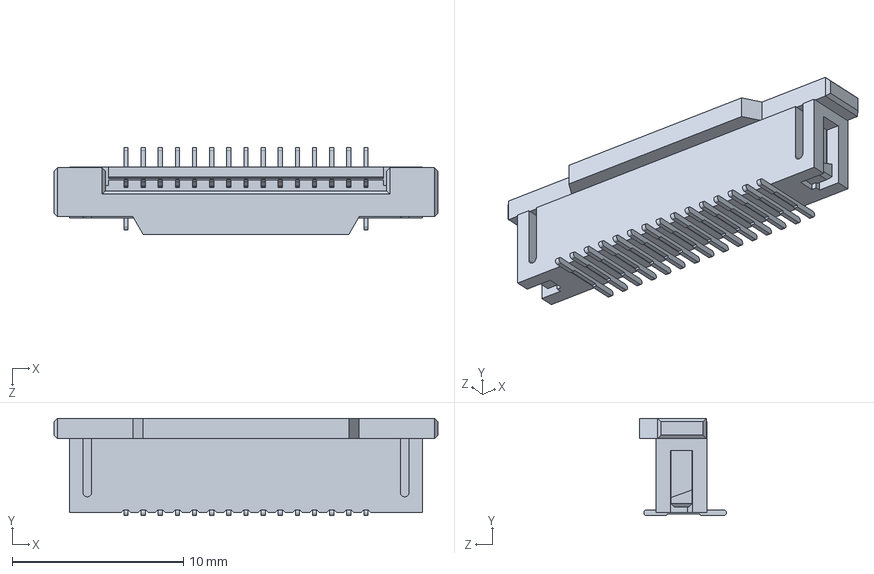
[picture p79: CAD file, 2020-09-08]
hardware/mechanics/solidworks/2019SP3.0/PCB-Tester-Board/Raspberry Pi 4B/Camera Connector, RPi4ModelB.SLDPRT
22.4 x 5.68 x 5.07 mm
