Semi-ATE/PCB-Tester/hardware/mechanics/solidworks/2019SP3.0/PCB-Tester-Board/Raspberry Pi 4B/Microphone Plug, RPi4ModelB.SLDPRT

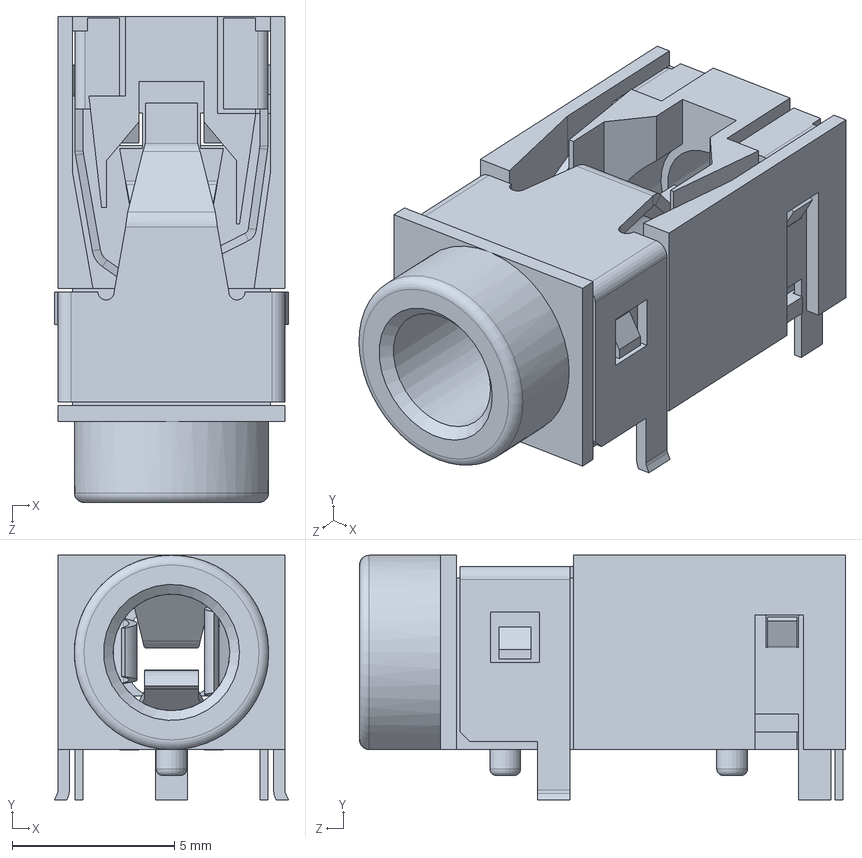
[picture p80: CAD file, 2020-09-08]
hardware/mechanics/solidworks/2019SP3.0/PCB-Tester-Board/Raspberry Pi 4B/Microphone Plug, RPi4ModelB.SLDPRT
7.23 x 7.55 x 15.0 mm
