Semi-ATE/PCB-Tester/hardware/mechanics/solidworks/2019SP3.0/housing/SHPSNA5_7.sldprt

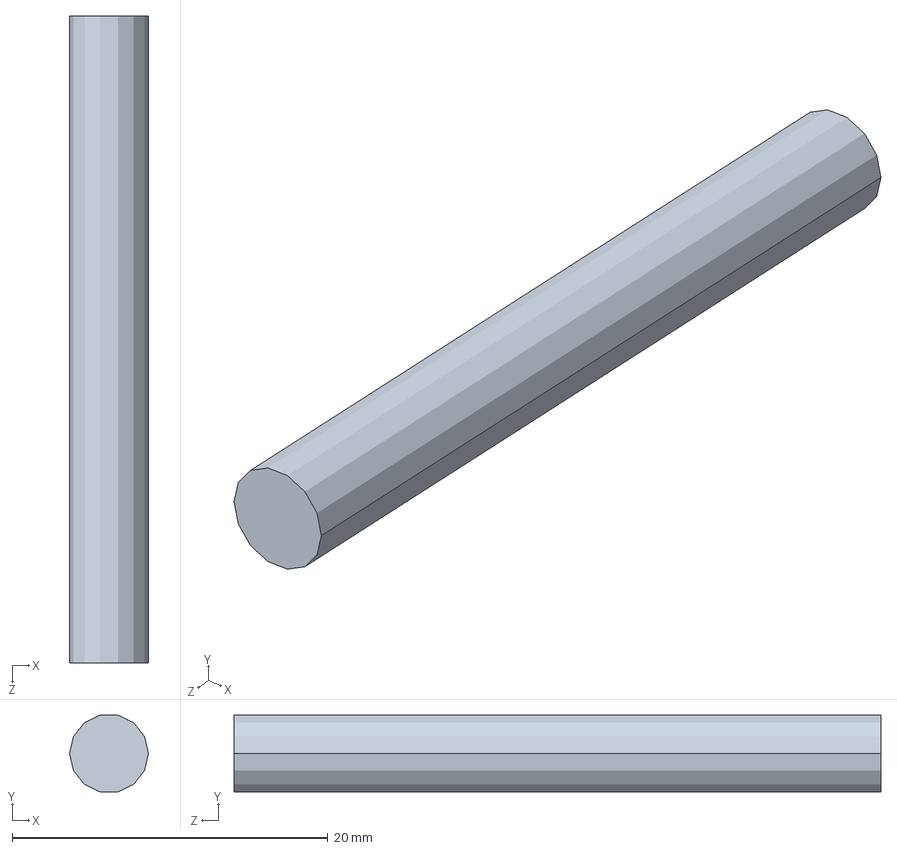
[picture p81: CAD file, 2020-09-08]
hardware/mechanics/solidworks/2019SP3.0/housing/SHPSNA5_7.sldprt
5.00 x 4.87 x 41.0 mm
