Semi-ATE/PCB-Tester/hardware/mechanics/solidworks/2019SP3.0/housing/SHPSNA5_5.sldprt

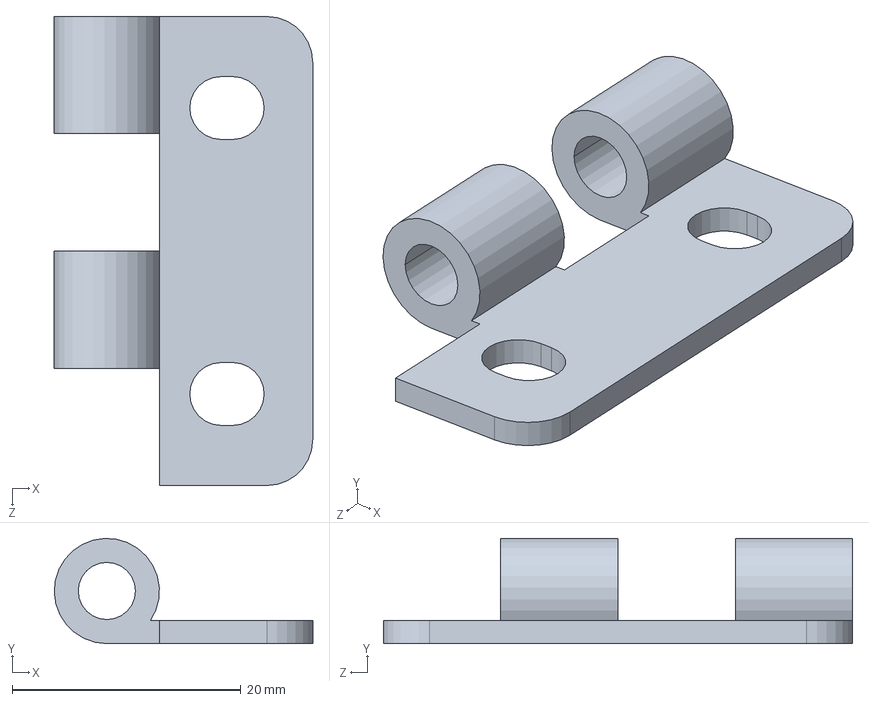
[picture p84: CAD file, 2020-09-08]
hardware/mechanics/solidworks/2019SP3.0/housing/SHPSNA5_5.sldprt
22.6 x 9.20 x 41.0 mm
