Semi-ATE/PCB-Tester/hardware/mechanics/solidworks/2019SP3.0/housing/DBGB5-17-5.sldprt

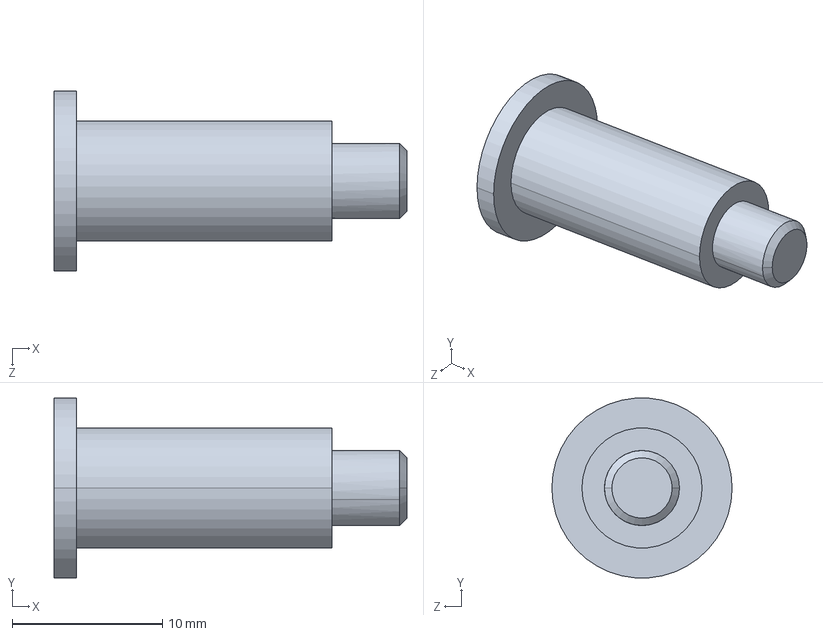
[picture p86: CAD file, 2020-09-08]
hardware/mechanics/solidworks/2019SP3.0/housing/DBGB5-17-5.sldprt
23.5 x 12.0 x 12.0 mm
