Semi-ATE/PCB-Tester/hardware/mechanics/solidworks/2019SP3.0/housing/SHPSNA5_3.sldprt

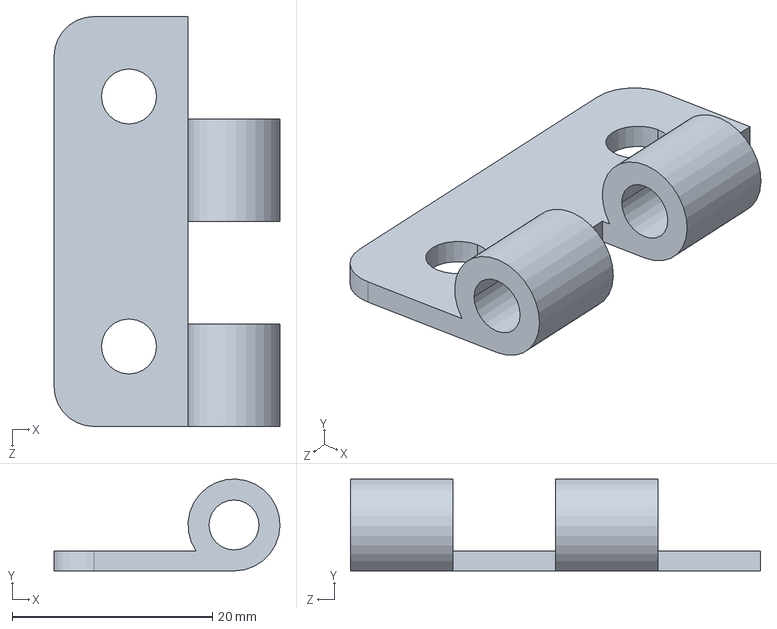
[picture p88: CAD file, 2020-09-08]
hardware/mechanics/solidworks/2019SP3.0/housing/SHPSNA5_3.sldprt
22.6 x 9.20 x 41.0 mm
