Semi-ATE/PCB-Tester/hardware/mechanics/solidworks/2019SP3.0/housing/Lever_top_right.STEP

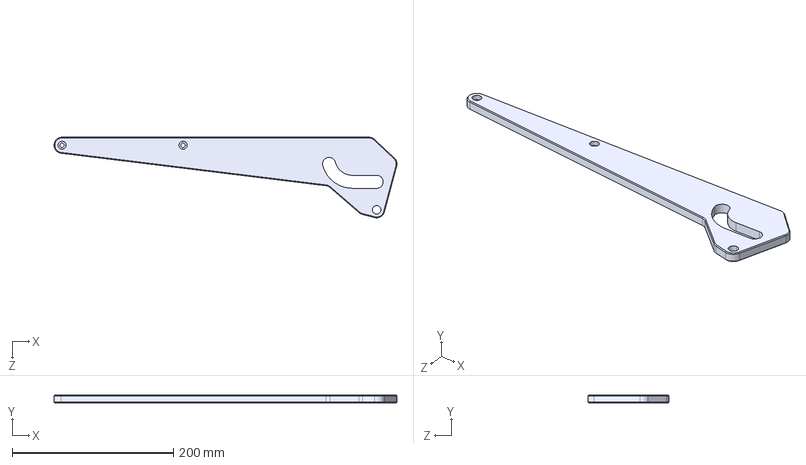
[picture p90: CAD file, 2020-09-08]
hardware/mechanics/solidworks/2019SP3.0/housing/Lever_top_right.STEP
425.2 x 10.0 x 100.0 mm
