Semi-ATE/PCB-Tester/hardware/mechanics/solidworks/2019SP3.0/housing/DBGB5-20-10.sldprt

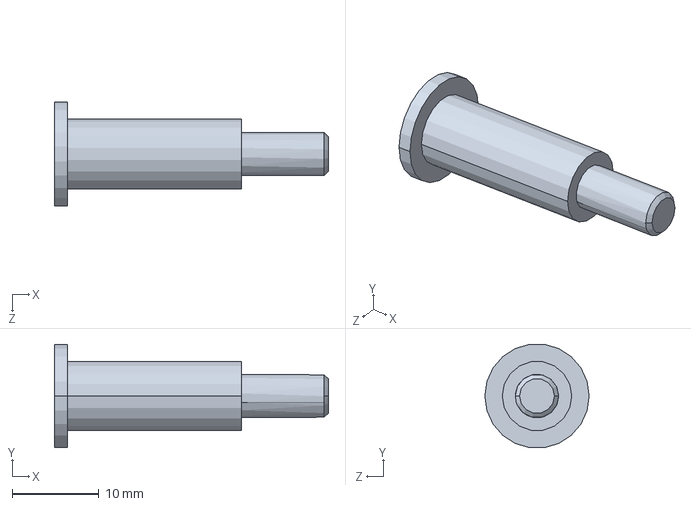
[picture p91: CAD file, 2020-09-08]
hardware/mechanics/solidworks/2019SP3.0/housing/DBGB5-20-10.sldprt
31.5 x 11.9 x 12.0 mm
