Semi-ATE/PCB-Tester/hardware/mechanics/solidworks/2019SP3.0/PCB-Tester-Board/Raspberry Pi 4B/SD Card Slot, RPi4ModelB.SLDPRT

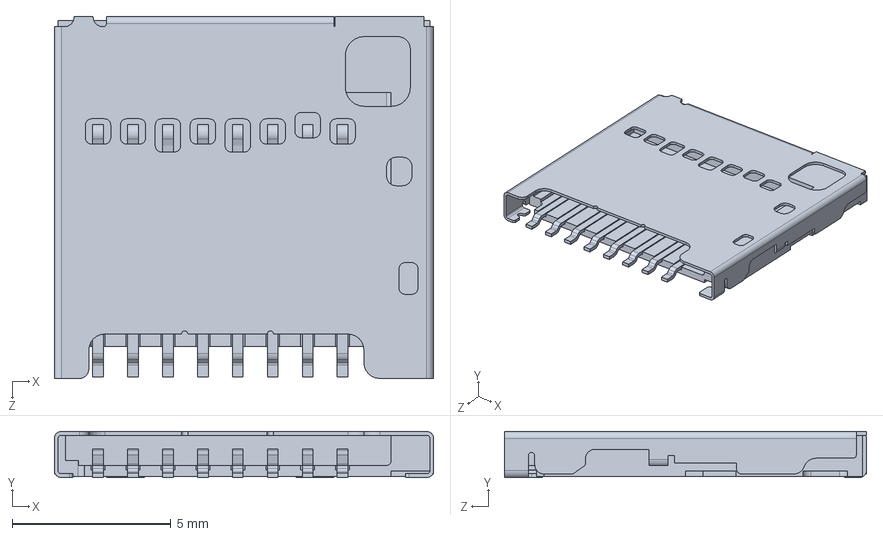
[picture p93: CAD file, 2020-09-08]
hardware/mechanics/solidworks/2019SP3.0/PCB-Tester-Board/Raspberry Pi 4B/SD Card Slot, RPi4ModelB.SLDPRT
11.9 x 1.45 x 11.4 mm
