Semi-ATE/PCB-Tester/hardware/mechanics/solidworks/2019SP3.0/housing/DBGB5-15-10.sldprt

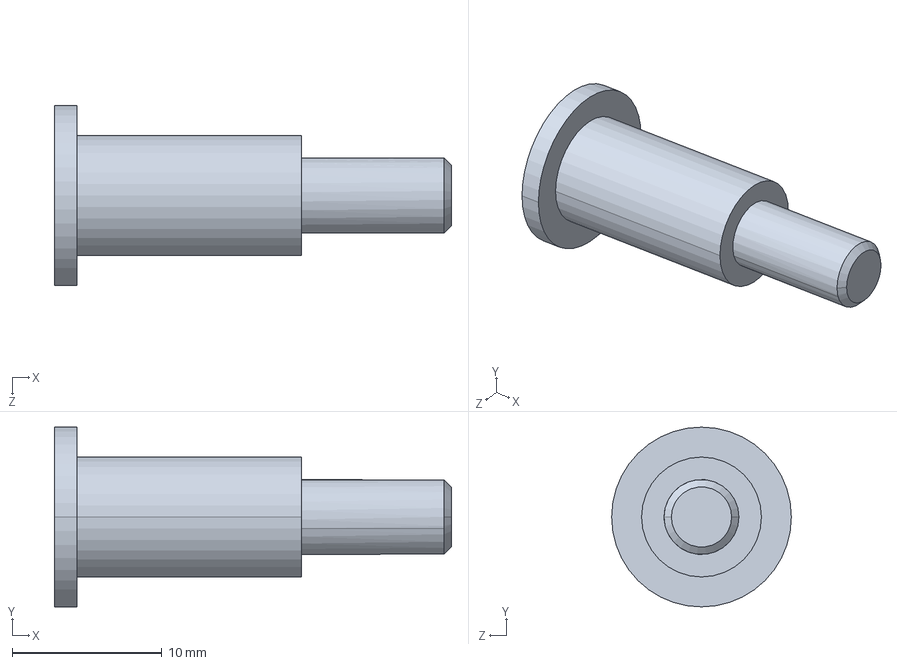
[picture p94: CAD file, 2020-09-08]
hardware/mechanics/solidworks/2019SP3.0/housing/DBGB5-15-10.sldprt
26.5 x 12.0 x 12.0 mm
