Semi-ATE/PCB-Tester/hardware/mechanics/solidworks/2019SP3.0/housing/FRNUT5.sldprt

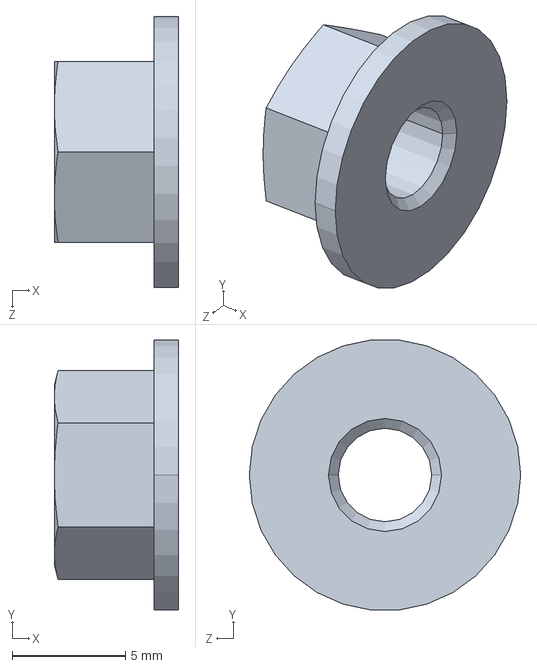
[picture p96: CAD file, 2020-09-08]
hardware/mechanics/solidworks/2019SP3.0/housing/FRNUT5.sldprt
5.50 x 11.9 x 12.0 mm
