Semi-ATE/PCB-Tester/hardware/mechanics/solidworks/2019SP3.0/PCB-Tester-Board/Raspberry Pi 4B/RPI-footprint.SLDPRT

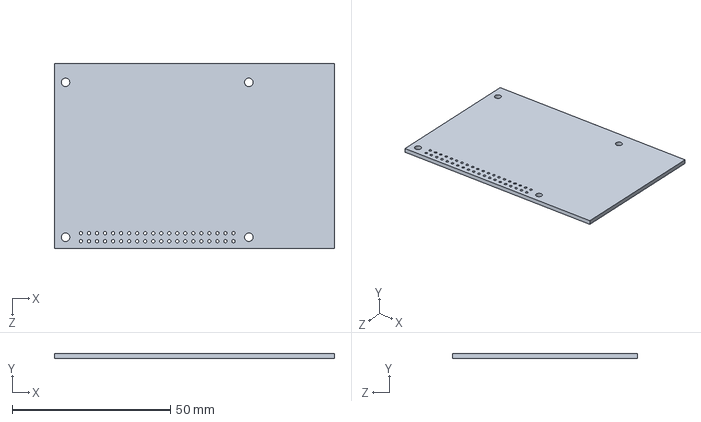
[picture p97: CAD file, 2020-04-20]
hardware/mechanics/solidworks/2019SP3.0/PCB-Tester-Board/Raspberry Pi 4B/RPI-footprint.SLDPRT
88.6 x 1.60 x 58.4 mm
