Semi-ATE/PCB-Tester/hardware/mechanics/solidworks/2019SP3.0/housing/Spindlehouse_left.STEP

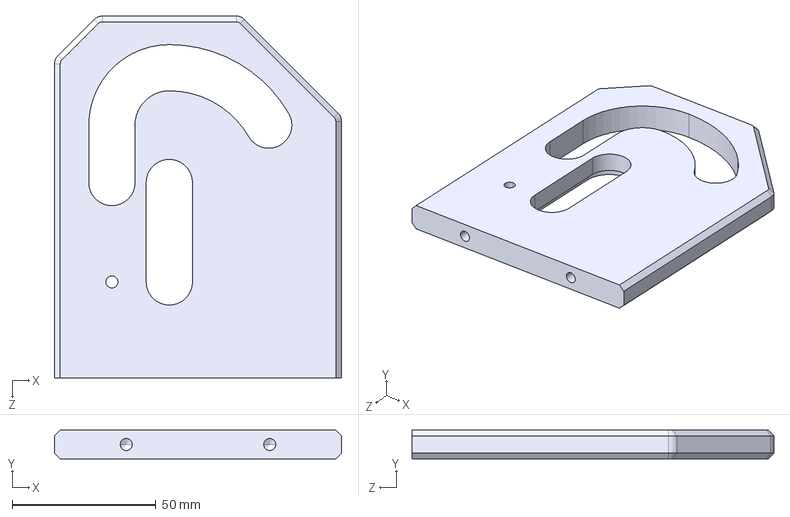
[picture p98: CAD file, 2020-09-08]
hardware/mechanics/solidworks/2019SP3.0/housing/Spindlehouse_left.STEP
100.0 x 10.0 x 126.1 mm
