Semi-ATE/PCB-Tester/hardware/mechanics/solidworks/2019SP3.0/housing/C-30-RK-18-black.SLDPRT

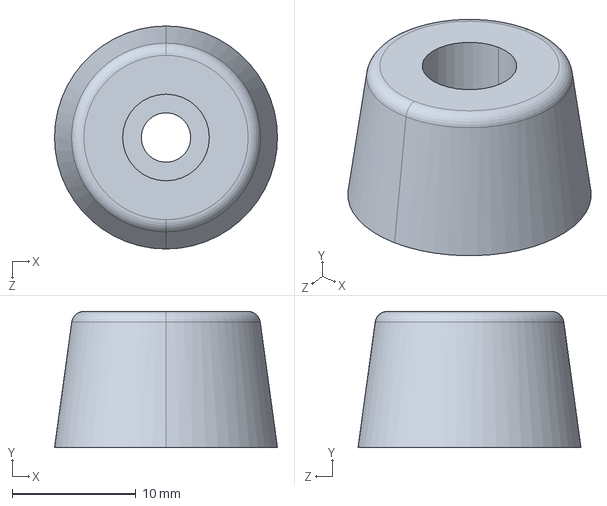
[picture p99: CAD file, 2020-09-08]
hardware/mechanics/solidworks/2019SP3.0/housing/C-30-RK-18-black.SLDPRT
18.0 x 11.0 x 18.0 mm
