Semi-ATE/PCB-Tester/hardware/mechanics/solidworks/2019SP3.0/housing/Handle.SLDPRT

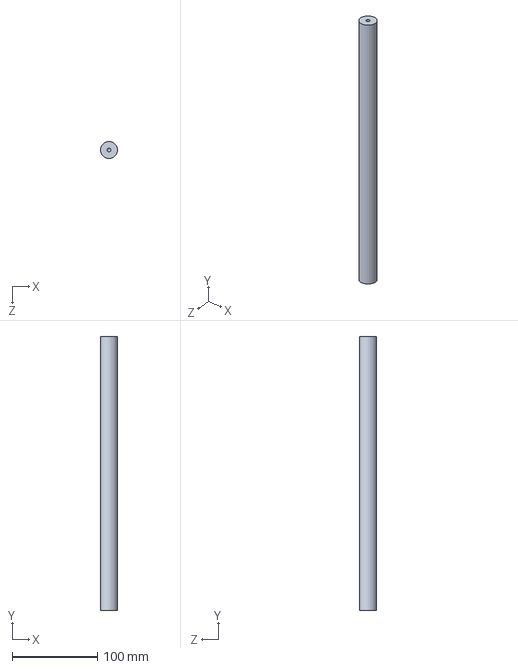
[picture p100: CAD file, 2020-09-08]
hardware/mechanics/solidworks/2019SP3.0/housing/Handle.SLDPRT
20.0 x 322.2 x 20.0 mm
