Semi-ATE/PCB-Tester/hardware/mechanics/solidworks/2019SP3.0/housing/FWHJ-D16.0-H20.0-V8.0-T1.5-L4.0.sldprt

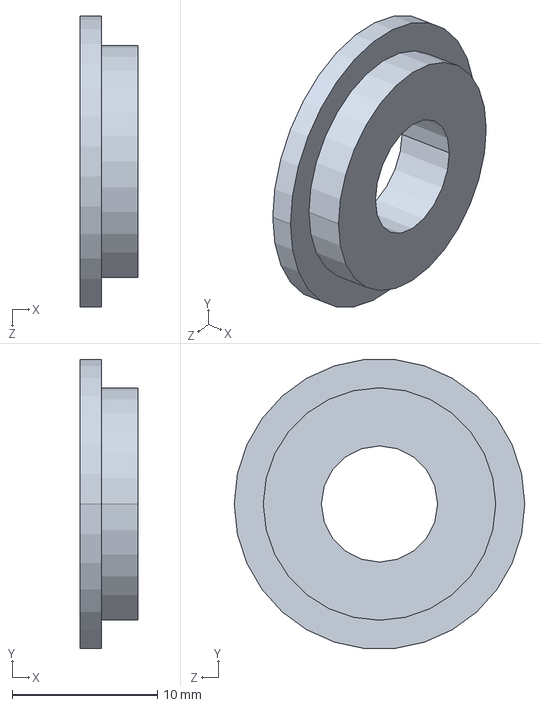
[picture p101: CAD file, 2020-09-08]
hardware/mechanics/solidworks/2019SP3.0/housing/FWHJ-D16.0-H20.0-V8.0-T1.5-L4.0.sldprt
4.00 x 19.9 x 20.0 mm
