Semi-ATE/PCB-Tester/hardware/mechanics/solidworks/2019SP3.0/housing/SWSJJ20-8-1.sldprt

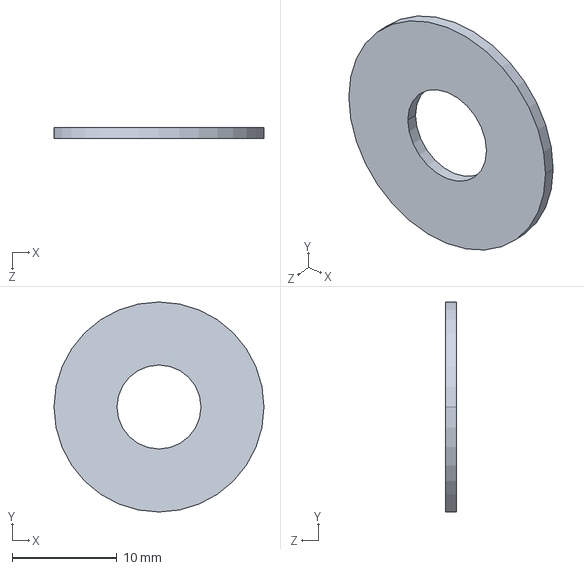
[picture p102: CAD file, 2020-09-08]
hardware/mechanics/solidworks/2019SP3.0/housing/SWSJJ20-8-1.sldprt
20.0 x 20.0 x 1.00 mm
