Semi-ATE/PCB-Tester/hardware/mechanics/solidworks/2019SP3.0/housing/FWHJ-D10.5-H16.0-V8.0-T1.5-L10.0.sldprt

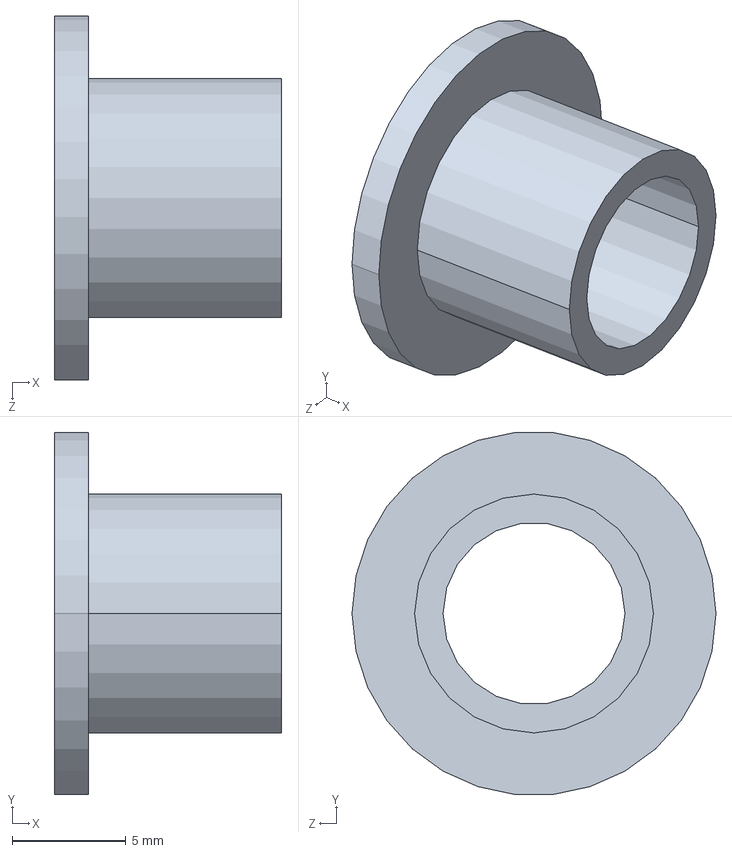
[picture p103: CAD file, 2020-09-08]
hardware/mechanics/solidworks/2019SP3.0/housing/FWHJ-D10.5-H16.0-V8.0-T1.5-L10.0.sldprt
10.0 x 15.9 x 16.0 mm
