Semi-ATE/PCB-Tester/hardware/mechanics/solidworks/2019SP3.0/housing/B688ZZ.sldprt

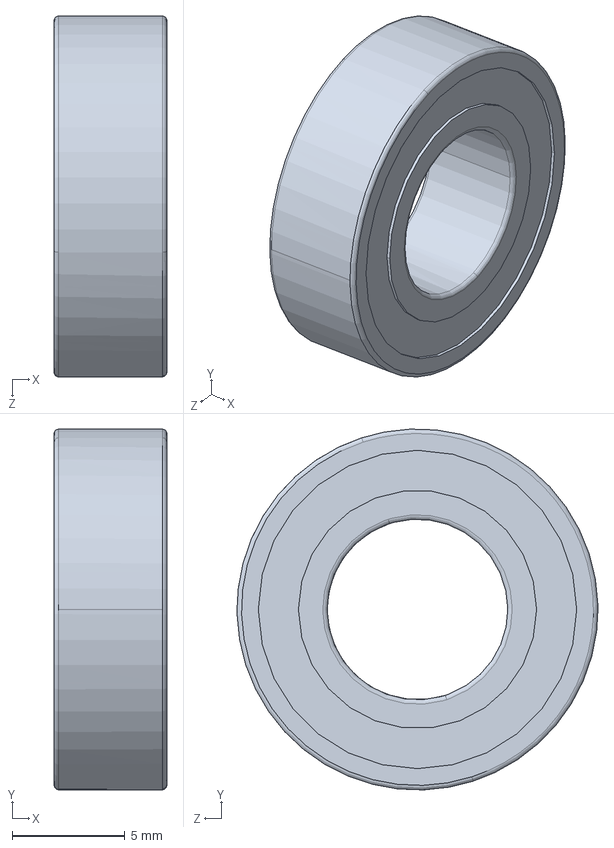
[picture p104: CAD file, 2020-09-08]
hardware/mechanics/solidworks/2019SP3.0/housing/B688ZZ.sldprt
5.00 x 16.0 x 16.0 mm
