Semi-ATE/PCB-Tester/hardware/mechanics/solidworks/2019SP3.0/PCB-Tester-Board/README.md

# PCB-Teester-Board

This directory holds the 3D model of the PCB-Tester-Board (extracted from Altium, or maunally made in solidworks)
