Semi-ATE/PCB-Tester/hardware/mechanics/solidworks/2019SP3.0/PCB-Tester-Board/M2.5x16 standoff/HSM2.5-6.4-16-2.JPG

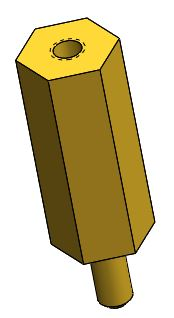
hardware/mechanics/solidworks/2019SP3.0/PCB-Tester-Board/M2.5x16 standoff/HSM2.5-6.4-16-2.JPG
